frank26080115/Hot-Wand/electrical/hot-wand.sch_preview.pdf

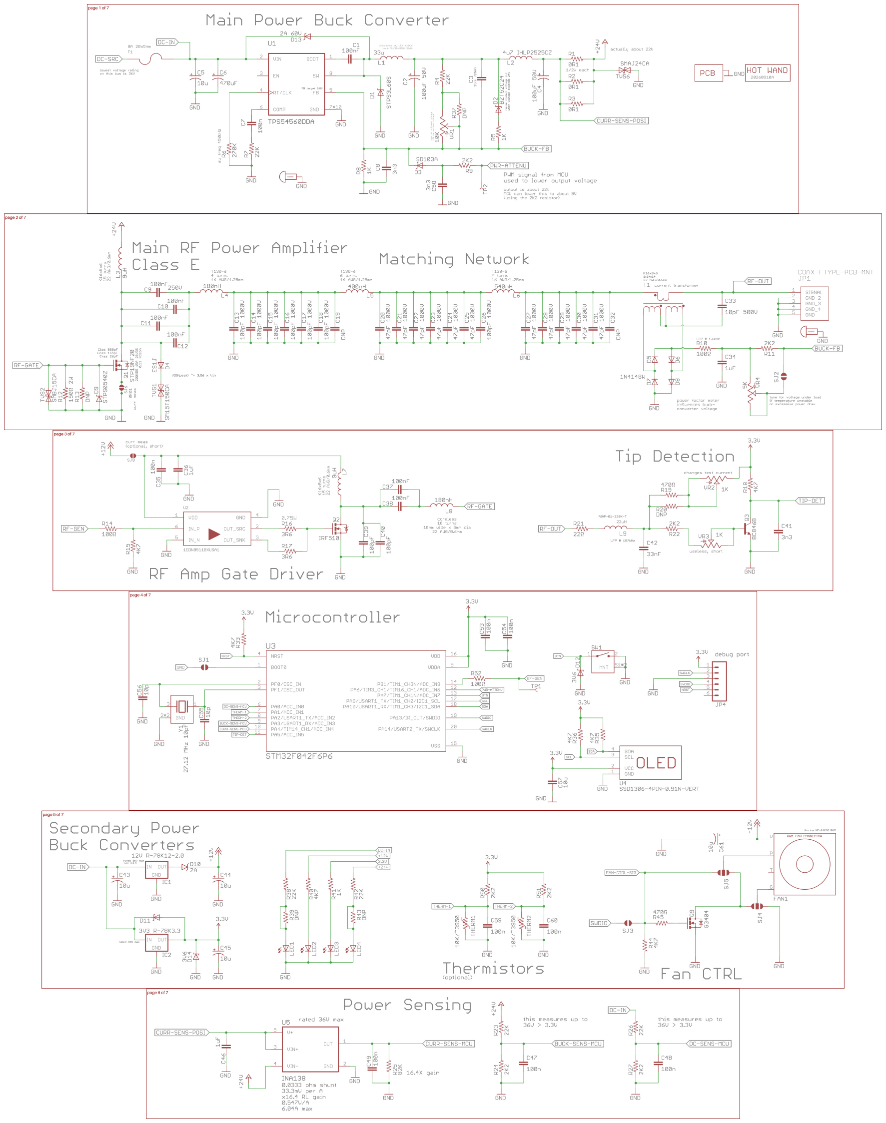
[picture p39: page 1]

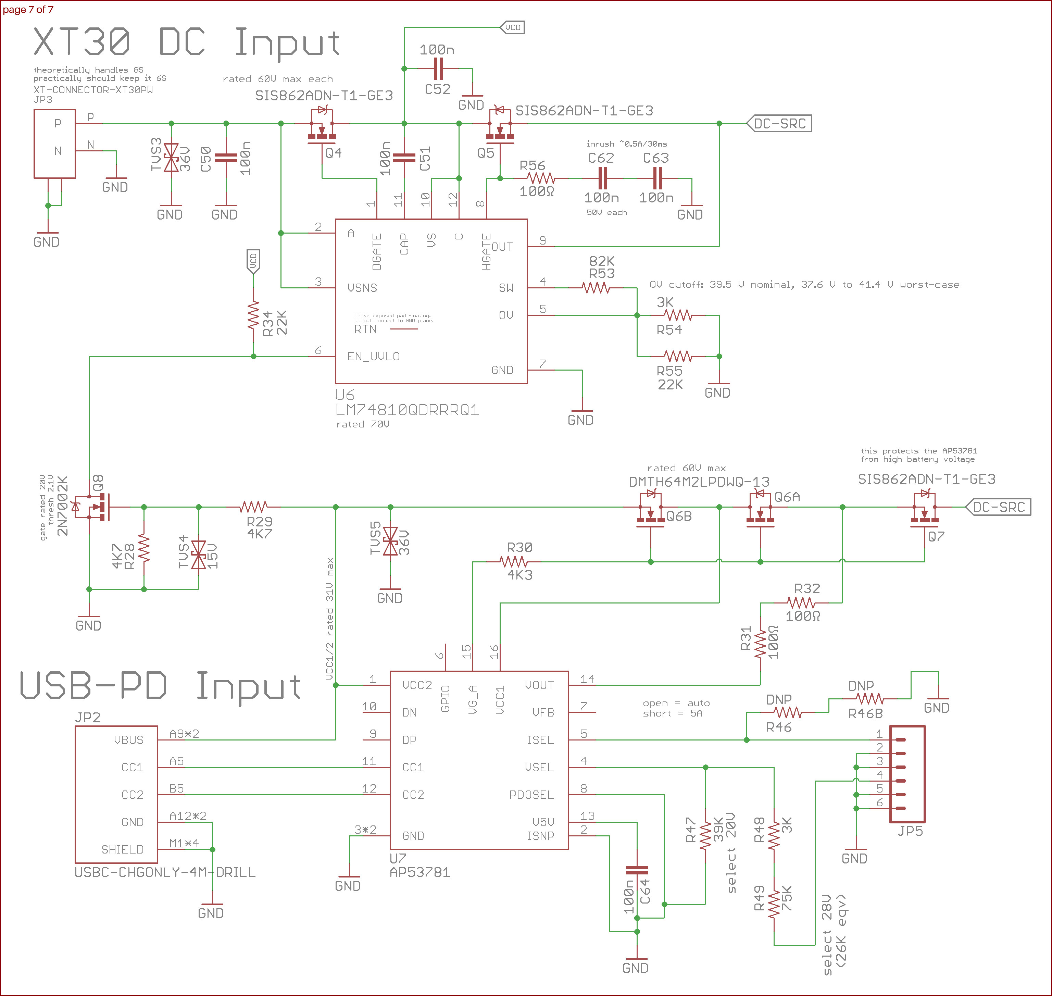
[picture p40: figure]
