frank26080115/Hot-Wand/electrical/hot-wand-lite.sch_preview.pdf

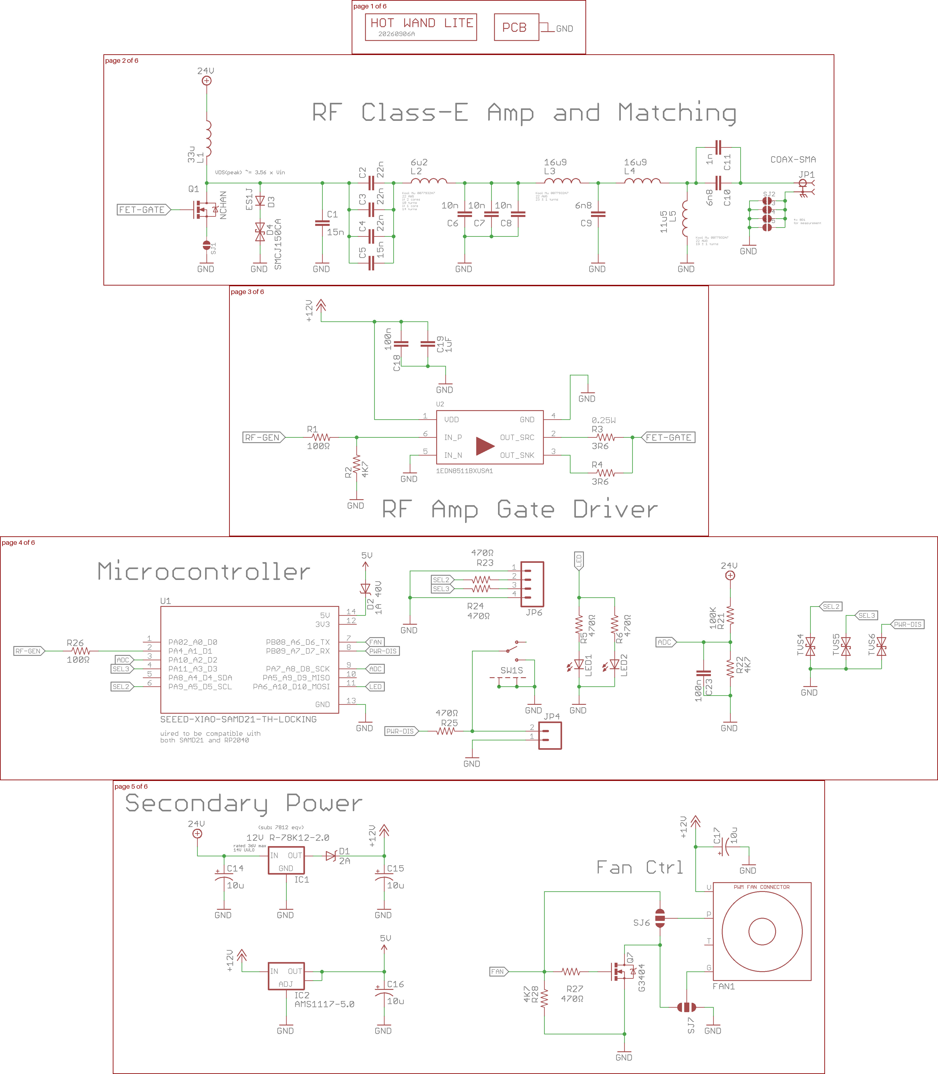
[picture p41: page 1]

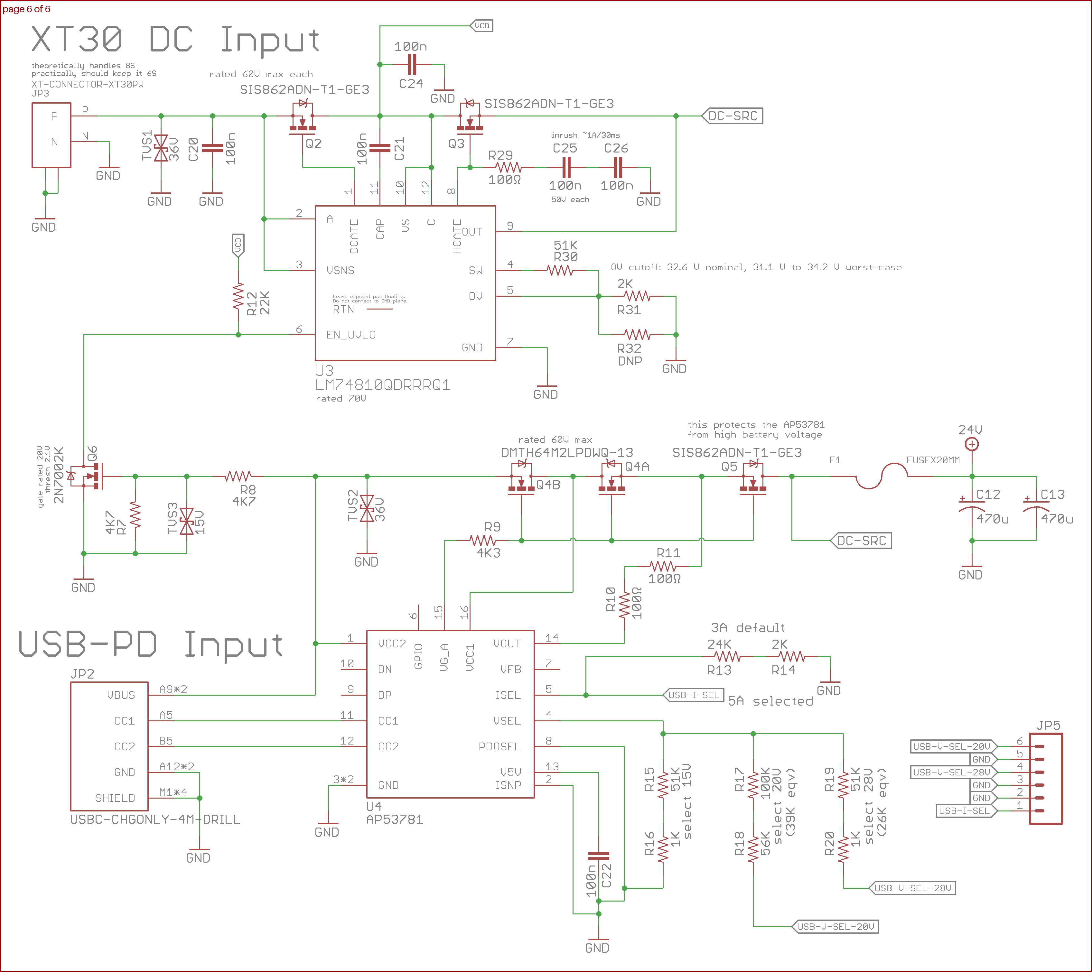
[picture p42: figure]
