frank26080115/Hot-Wand/doc/design-study/sim-470khz/overtemperature/duty.csv

label | tip | frequency_Hz | ptip | pin | pq | vpeak | vturn_3V | vturn_max_3V | iq_peak | cout_rms_A | cout_peak_V | settle_change
D30 | cold | 470000.0 | 15.2460892255 | 31.6820685661 | 13.6332232027 | 66.0378219717 | 58.740601634491824 | 58.790650806476826 | 91.74689067939352 | 1.1465155950586285 | 77.86099760184408 | -0.0002586320019942745
D35 | cold | 470000.0 | 27.8511892675 | 44.5464677931 | 12.4165617244 | 73.4204599296 | 52.99617693522123 | 53.034207180420864 | 84.26761203744175 | 1.5496114778329617 | 103.50217958498992 | 6.62253613330499e-05
D40 | cold | 470000.0 | 43.839329264 | 59.0112184001 | 9.07199362702 | 79.0444573505 | 40.348435256897474 | 40.38910875670194 | 67.48741435793191 | 1.944164979972991 | 125.91700755865497 | 0.00023527174681081675
D45 | cold | 470000.0 | 58.3940621923 | 71.6314488854 | 5.44397941609 | 83.6173232381 | 22.32048153011515 | 22.348759915549376 | 43.61757043852841 | 2.2438069070625146 | 143.65586091826634 | 4.348289923683524e-06
D47.5 | cold | 470000.0 | 63.1862314165 | 75.8699553154 | 4.30991338751 | 85.0733932421 | 12.956661549493777 | 12.975770965911684 | 30.13291947995617 | 2.3340615523982677 | 149.12999289719176 | 3.3242024291002537e-05
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
