frank26080115/Hot-Wand/doc/design-study/sim-470khz/overtemperature/inductors.csv

label | tip | frequency_Hz | ptip | pin | pq | vpeak | vturn_3V | vturn_max_3V | iq_peak | cout_rms_A | cout_peak_V | settle_change
baseline | cold | 470000.0 | 65.7724614815 | 78.2634268863 | 3.78757391316 | 85.8123798694 | 4.903648211298206 | 4.911344844539766 | 30.13291947995617 | 2.381348449450267 | 152.02446680378642 | -1.7534833572918629e-06
L2_-5% | cold | 470000.0 | 74.8583306088 | 91.3728903754 | 6.20488874992 | 82.5457297478 | 18.560682668685228 | 18.59483694554503 | 36.75802010978948 | 2.5405185681576437 | 161.5283471495771 | 0.0001229292416855543
L2_+2% | cold | 470000.0 | 60.7891149073 | 71.9417979183 | 3.22813133709 | 86.2358808974 | 1.4561562750915082 | 1.4658743464604655 | 30.70574819863137 | 2.2893585767824733 | 146.5096551716814 | 2.010327300627779e-06
L2_+5% | cold | 470000.0 | 53.1964953746 | 62.6157434585 | 2.62191636593 | 87.0986545869 | -0.7160607807450767 | -0.7142148700238609 | 30.602989040333167 | 2.1416195234743243 | 138.15701628123037 | 2.0345637539165295e-06
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
