frank26080115/Hot-Wand/doc/design-study/imgs/current_transformer_plots/90.png

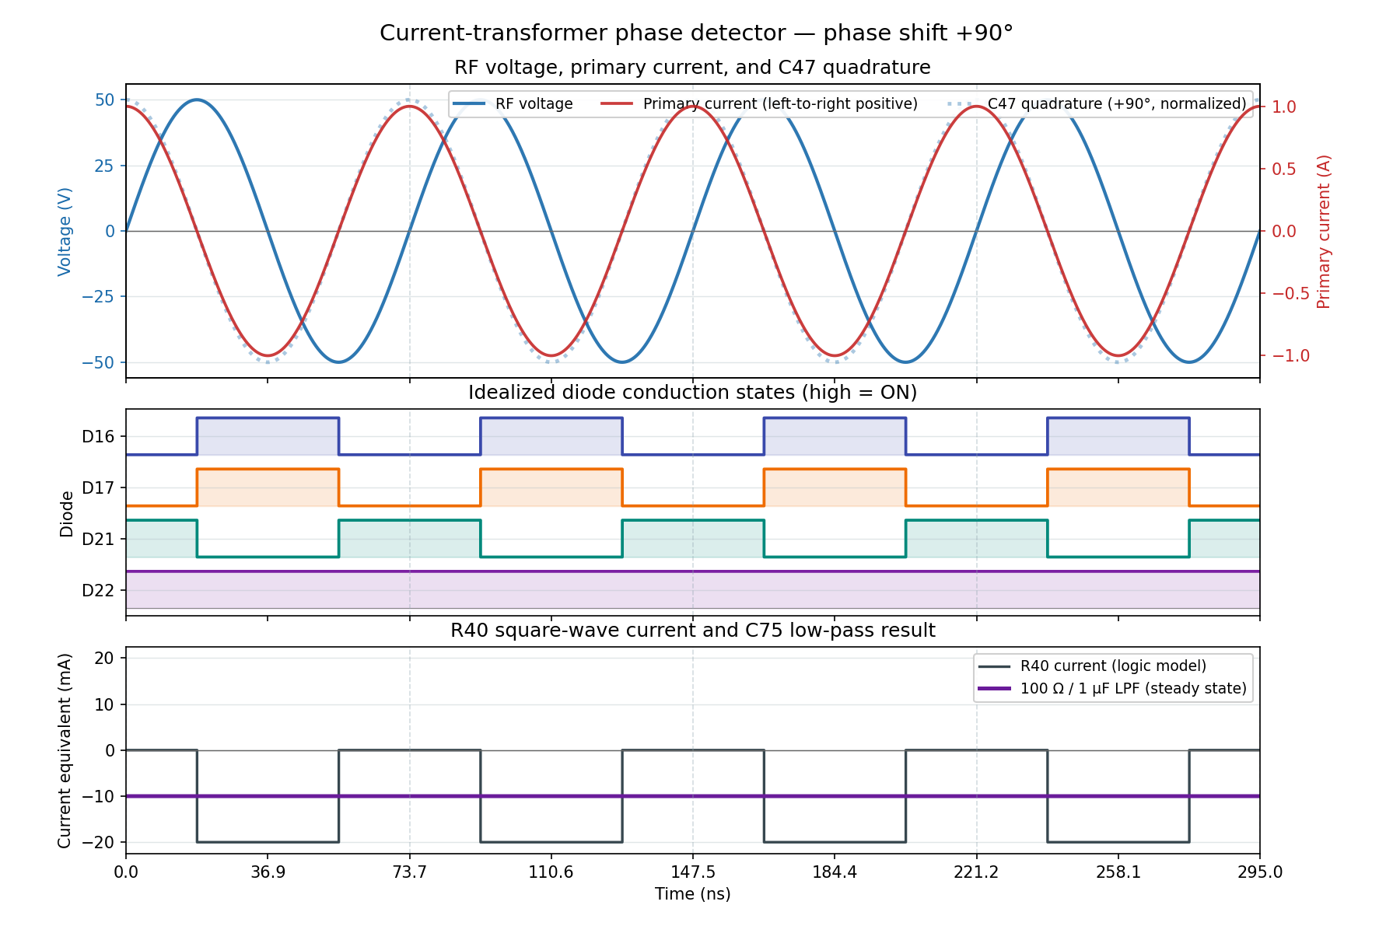
doc/design-study/imgs/current_transformer_plots/90.png
