frank26080115/Hot-Wand/doc/design-study/imgs/current_transformer_plots/225.png

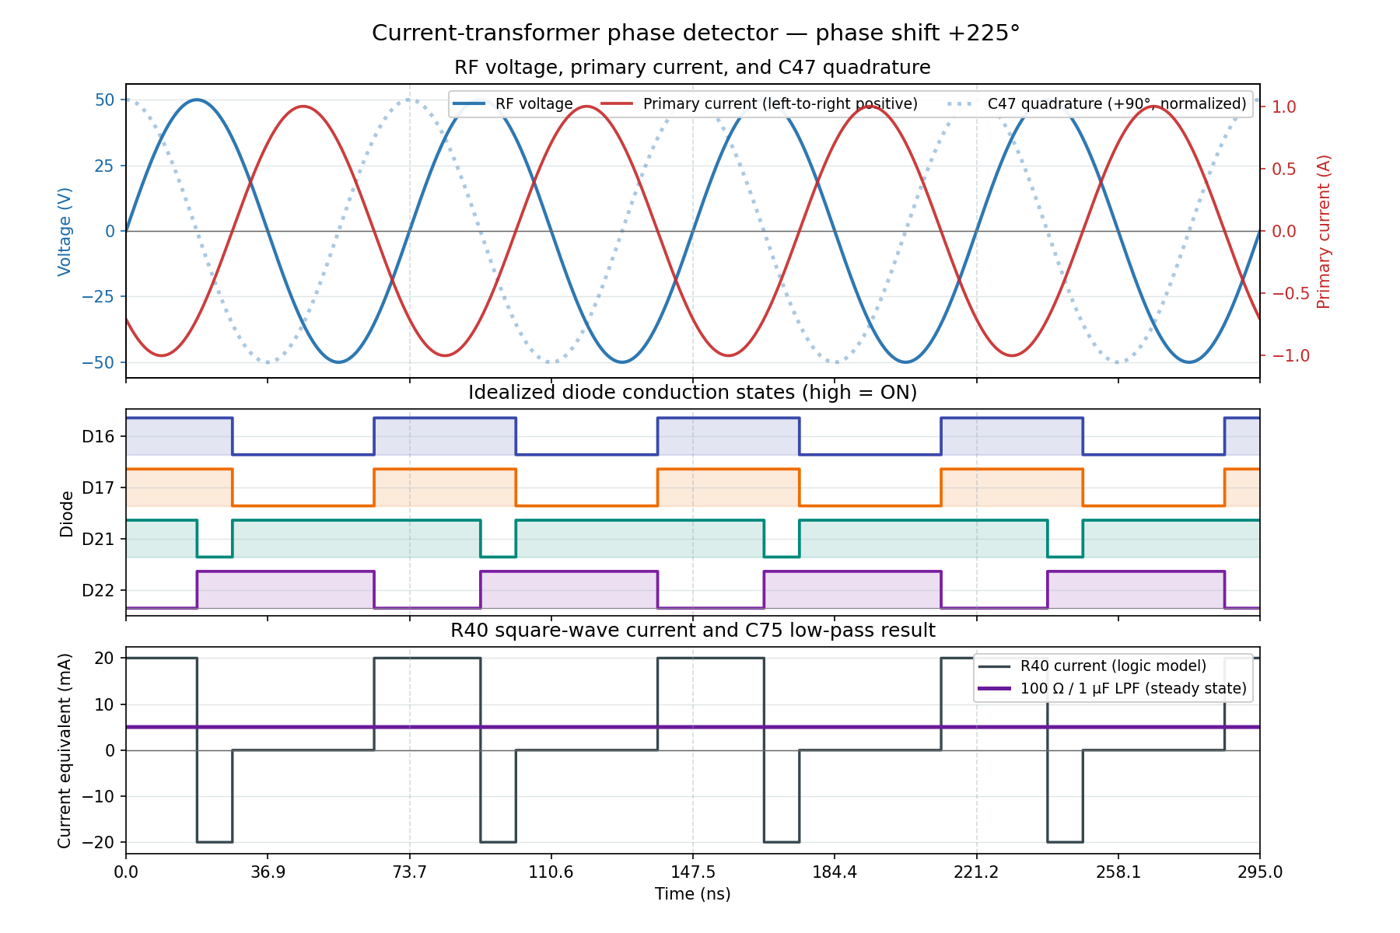
doc/design-study/imgs/current_transformer_plots/225.png
