frank26080115/Hot-Wand/doc/design-study/imgs/current_transformer_plots/345.png

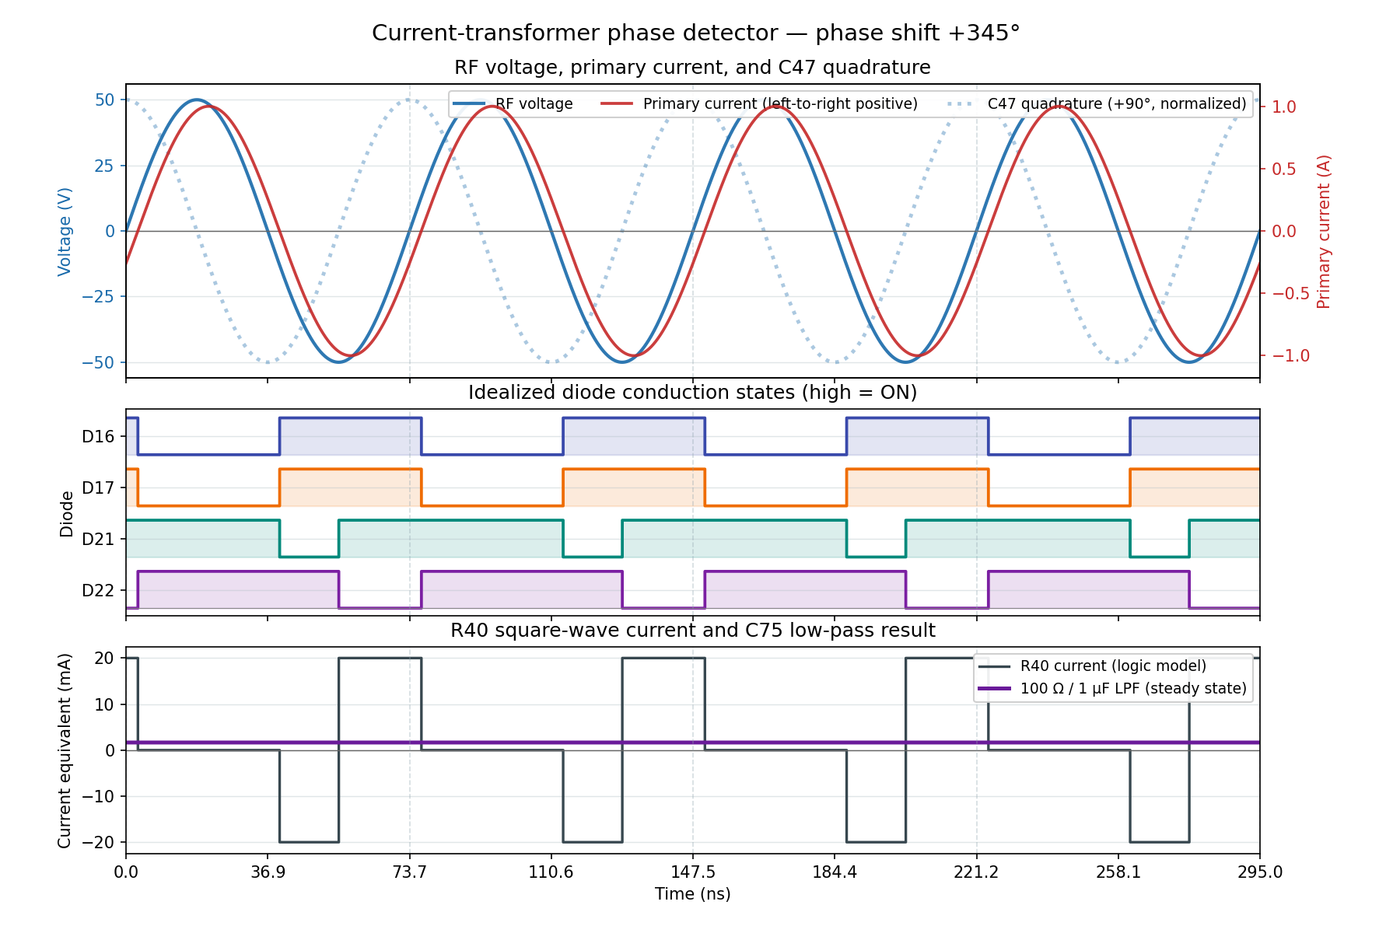
doc/design-study/imgs/current_transformer_plots/345.png
