frank26080115/Hot-Wand/doc/design-study/imgs/tip_det_sim.png

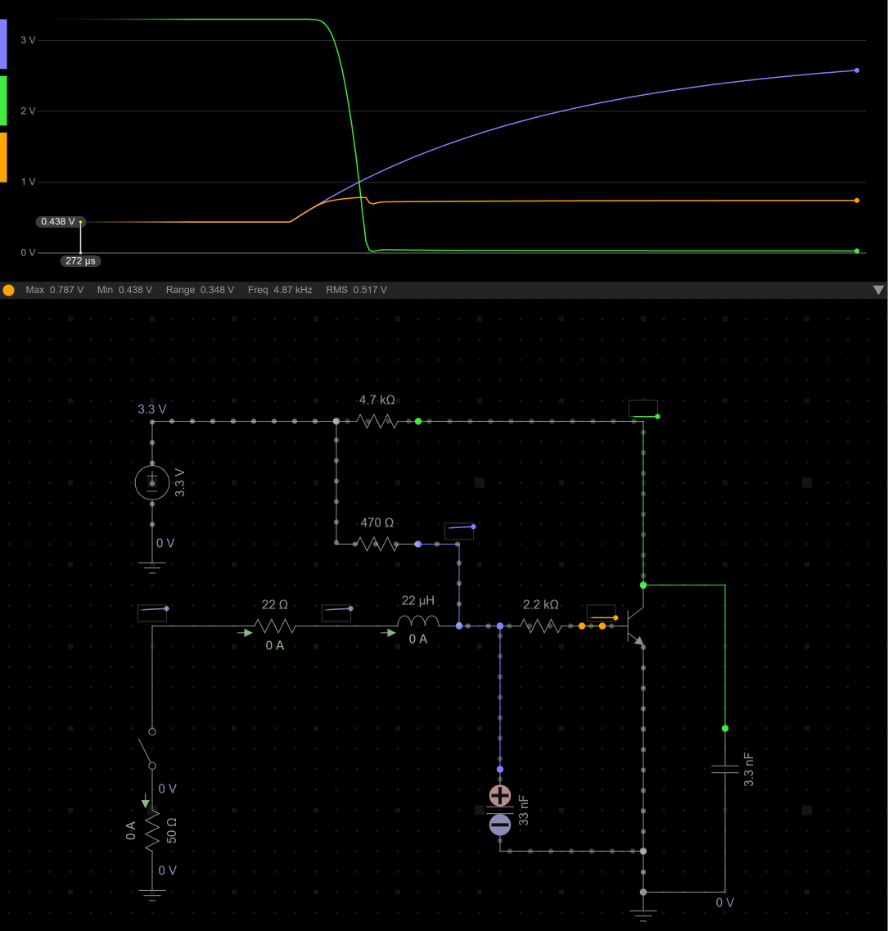
doc/design-study/imgs/tip_det_sim.png
