frank26080115/Hot-Wand/doc/imgs/stand/side_view.png

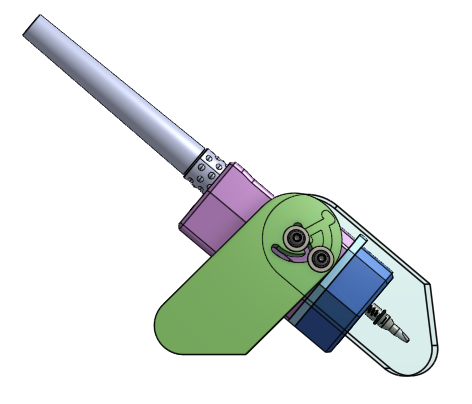
doc/imgs/stand/side_view.png
