frank26080115/Hot-Wand/electrical/mfg-lite/gerbers/illustration-bottom-mirrored.png

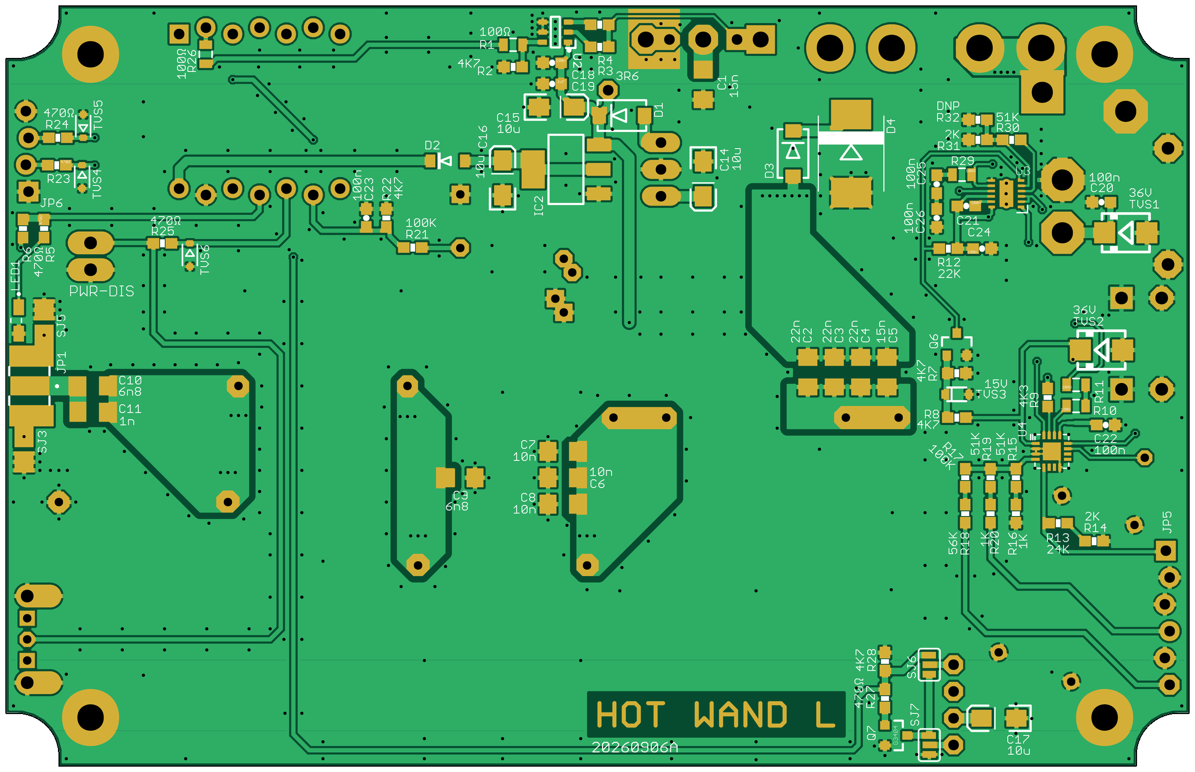
electrical/mfg-lite/gerbers/illustration-bottom-mirrored.png
