frank26080115/Hot-Wand/electrical/mfg-lite/gerbers/illustration-top.png

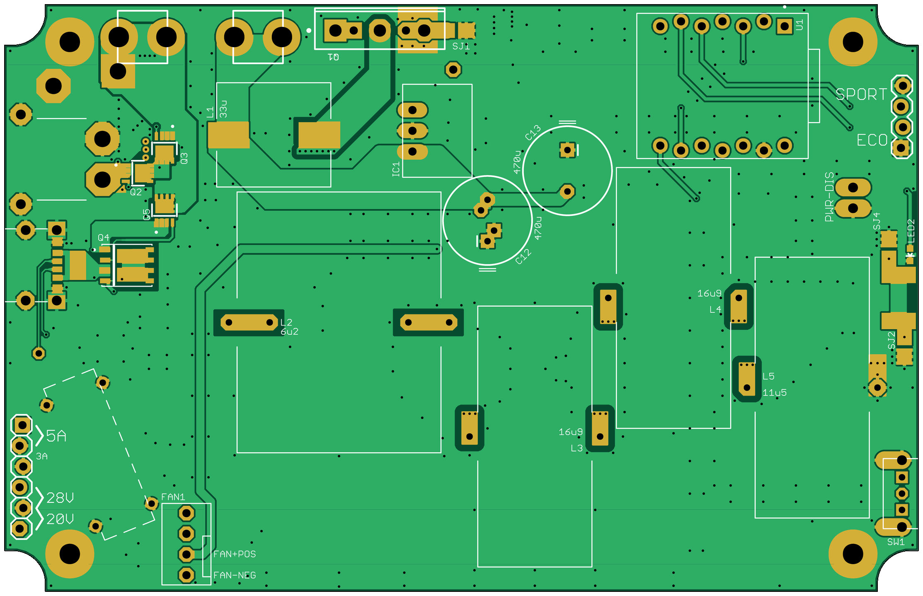
electrical/mfg-lite/gerbers/illustration-top.png
