frank26080115/Hot-Wand/electrical/mfg-lite/gerbers/preview-bottom.png

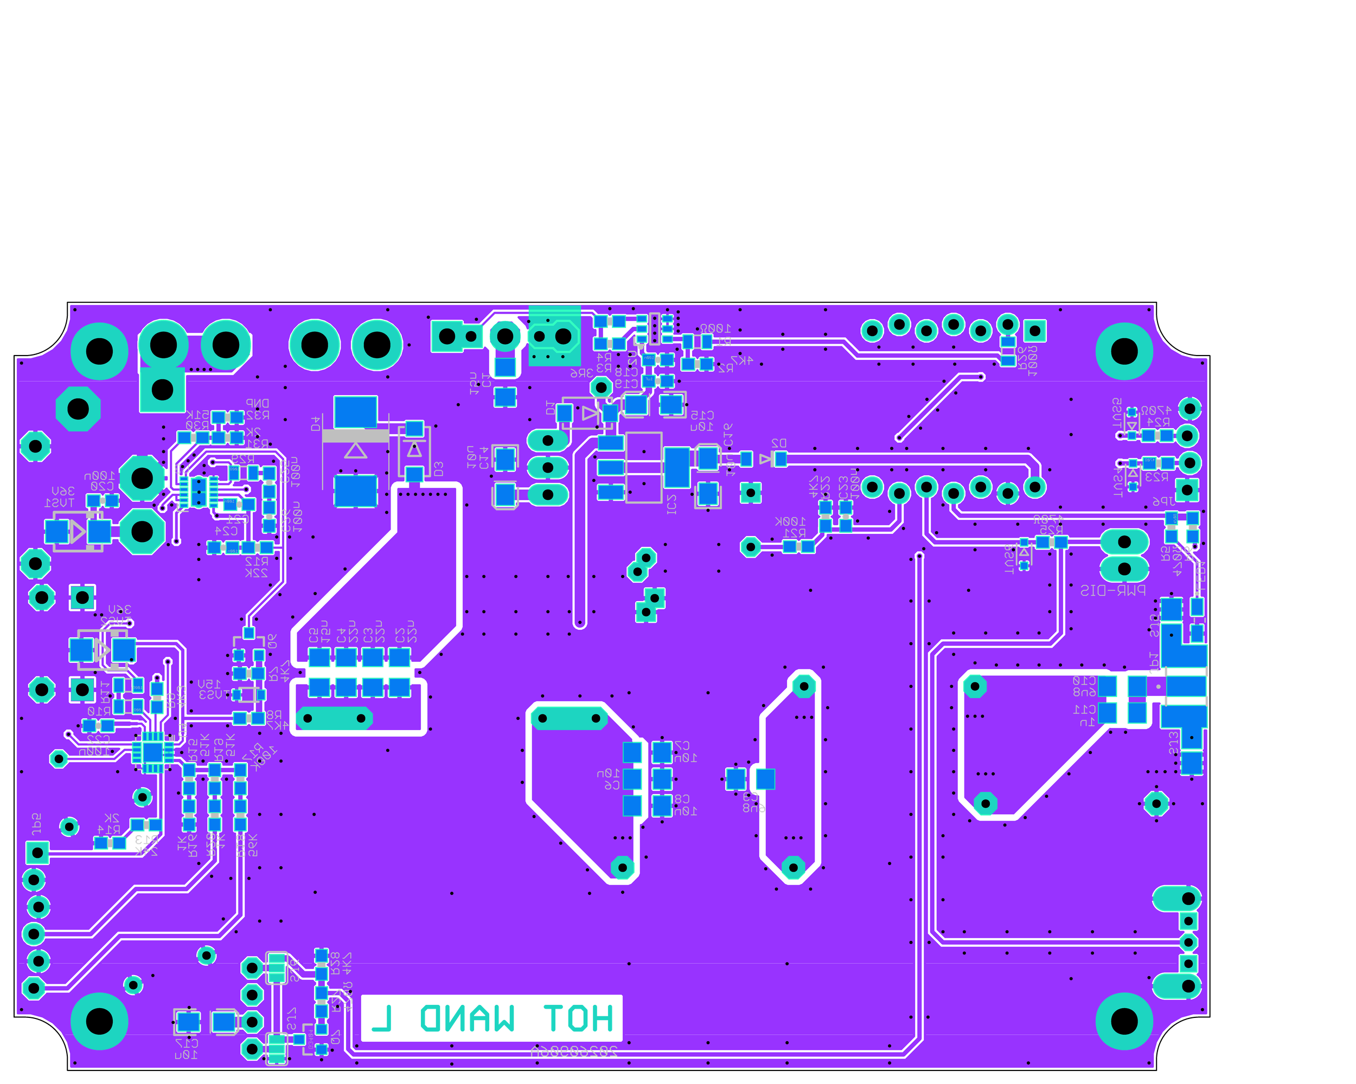
electrical/mfg-lite/gerbers/preview-bottom.png
