frank26080115/Hot-Wand/electrical/mfg-lite/gerbers/preview-top.png

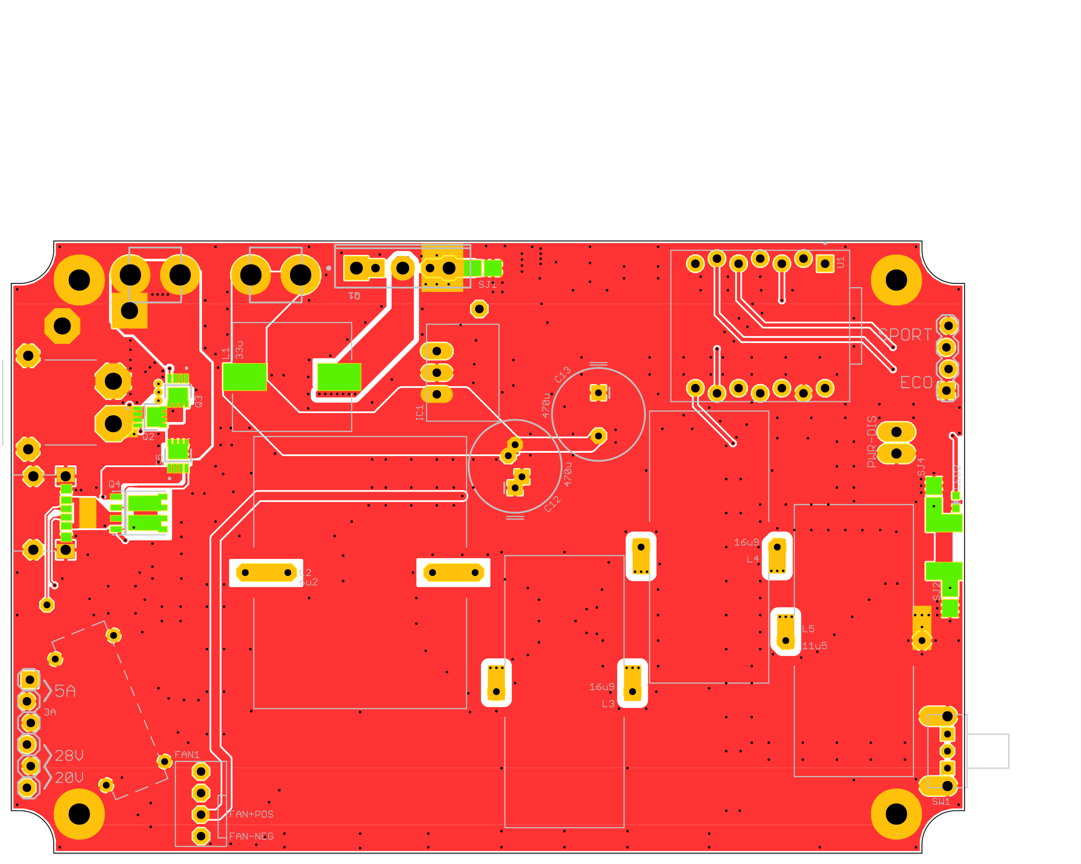
electrical/mfg-lite/gerbers/preview-top.png
