frank26080115/Hot-Wand/electrical/mfg/gerbers/illustration-bottom-mirrored.png

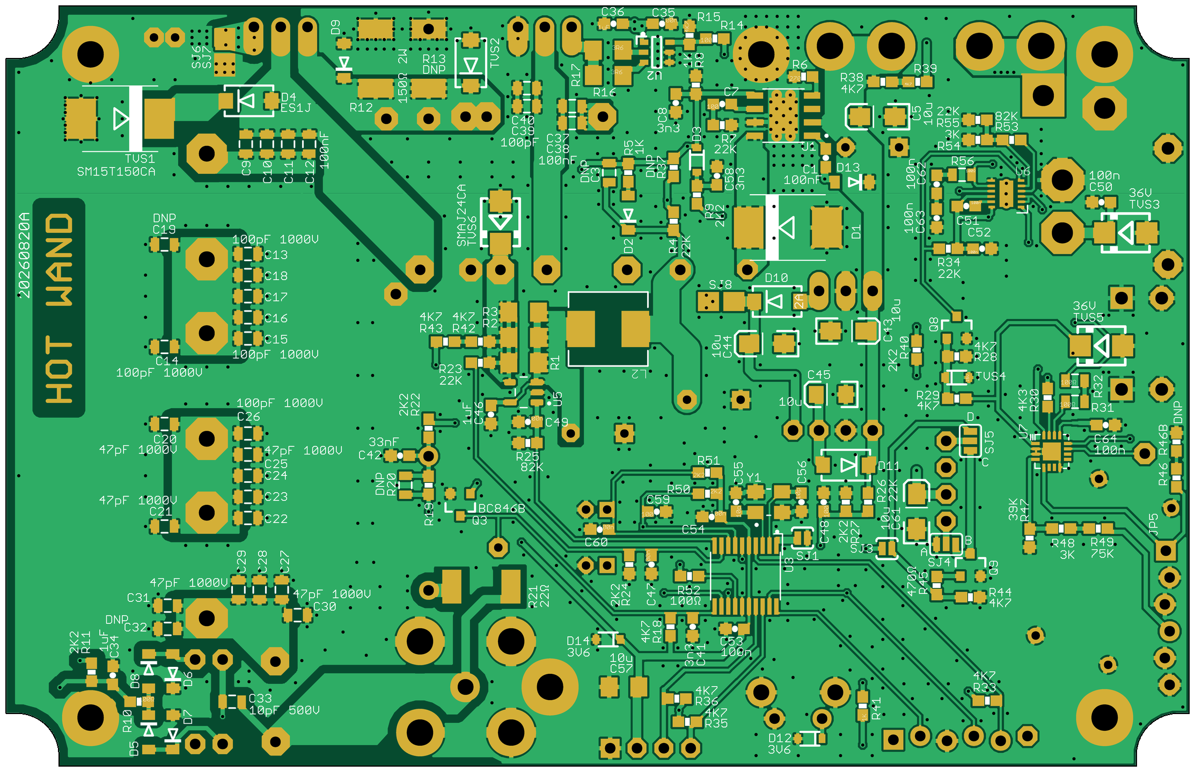
electrical/mfg/gerbers/illustration-bottom-mirrored.png
