frank26080115/Hot-Wand/electrical/mfg/gerbers/illustration-top.png

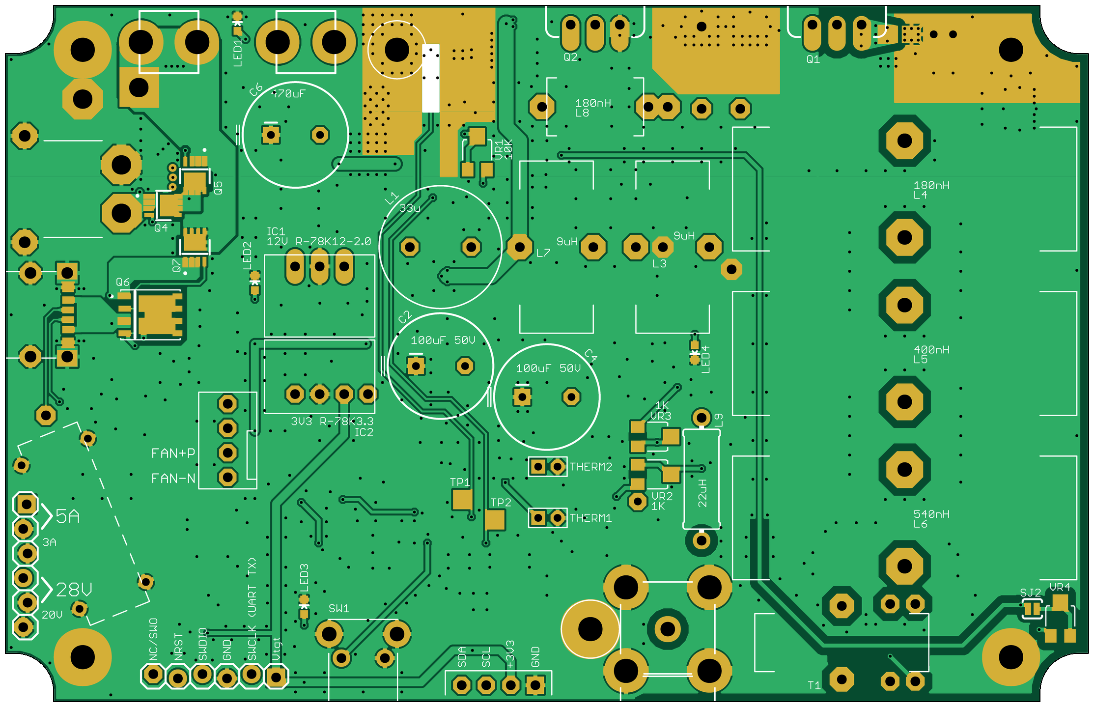
electrical/mfg/gerbers/illustration-top.png
