frank26080115/Hot-Wand/electrical/mfg/gerbers/preview-bottom-mirrored.png

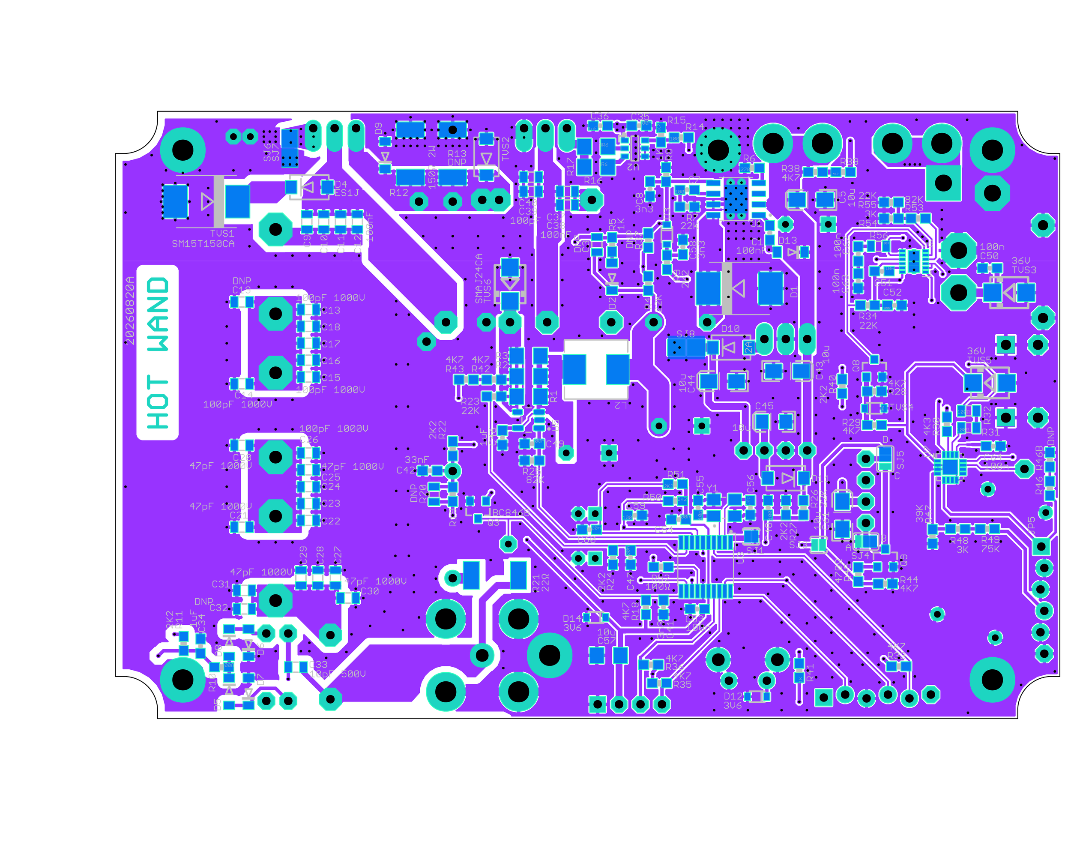
electrical/mfg/gerbers/preview-bottom-mirrored.png
