frank26080115/Hot-Wand/electrical/mfg/gerbers/preview-bottom.png

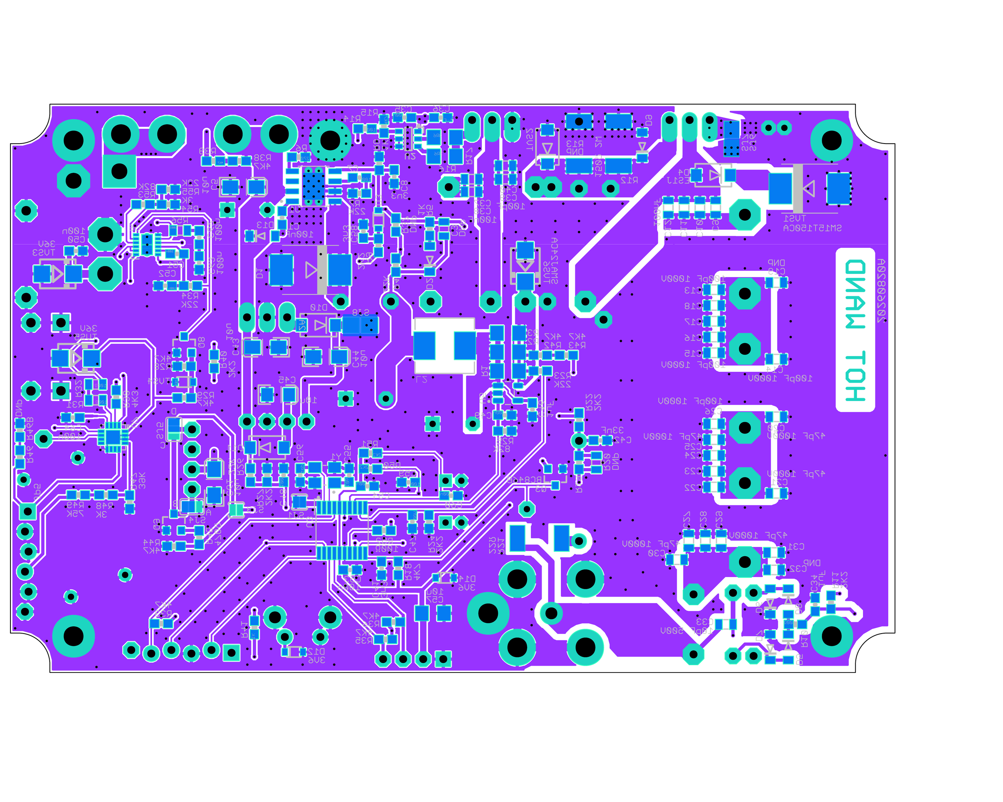
electrical/mfg/gerbers/preview-bottom.png
