frank26080115/Hot-Wand/electrical/mfg/gerbers/preview-top.png

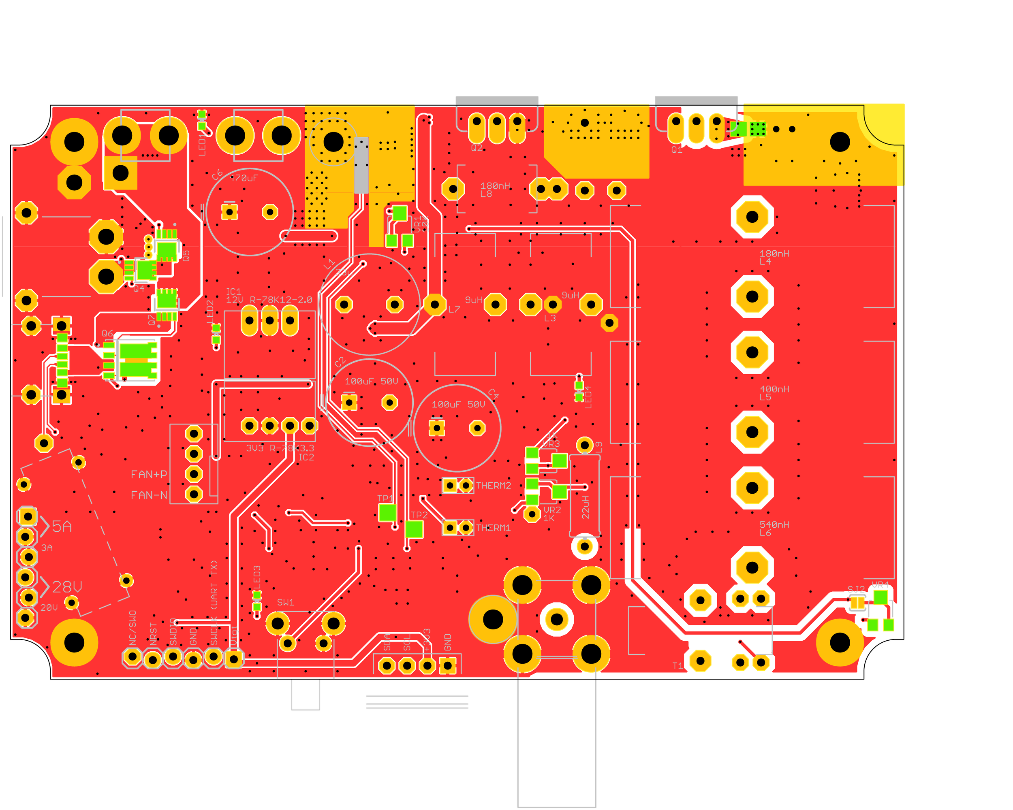
electrical/mfg/gerbers/preview-top.png
