frank26080115/Hot-Wand/firmware/art/fiducial_x8.png

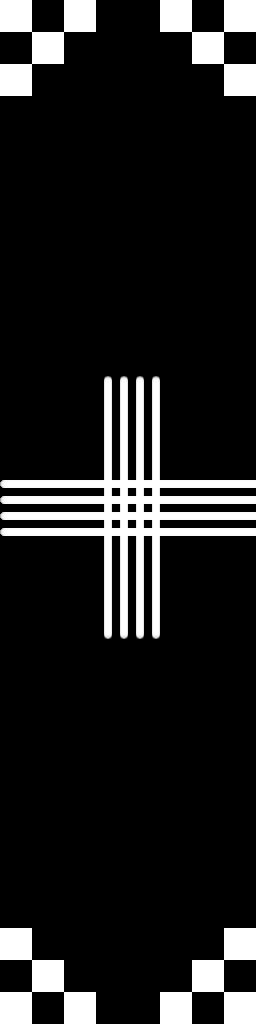
firmware/art/fiducial_x8.png
