frank26080115/Hot-Wand/doc/imgs-shopping/small/zipties.jpg

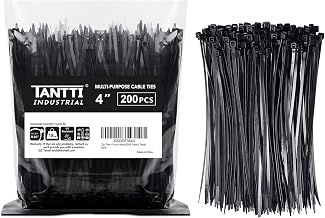
doc/imgs-shopping/small/zipties.jpg
