frank26080115/Hot-Wand/mechanical/main/heatsink-exhaust-duct.step

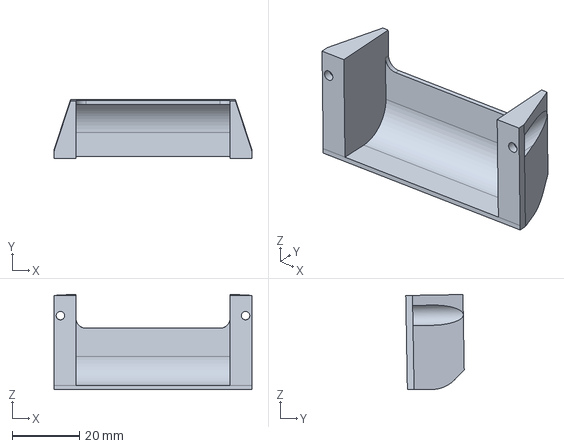
[picture p141: CAD file, 2026-09-05]
mechanical/main/heatsink-exhaust-duct.step
58.8 x 17.4 x 28.2 mm
