frank26080115/Hot-Wand/mechanical/stand/alu-strike-plate.step

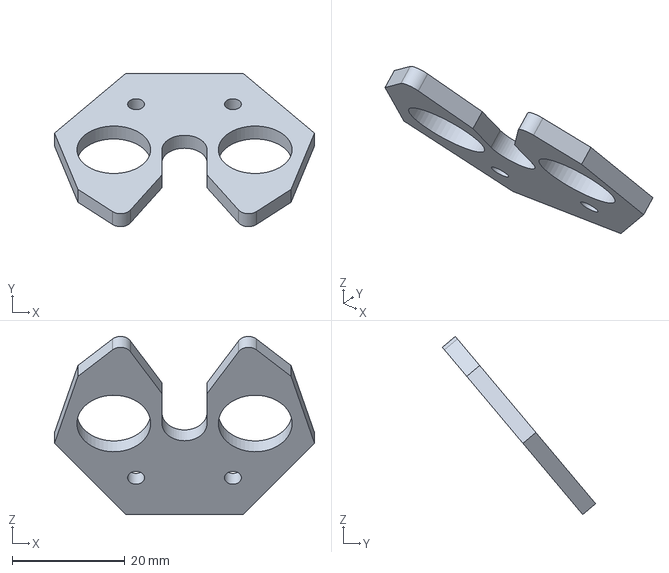
[picture p142: CAD file, 2026-09-03]
mechanical/stand/alu-strike-plate.step
46.1 x 27.2 x 31.6 mm
