frank26080115/Hot-Wand/mechanical/main/air-intake-grille.step

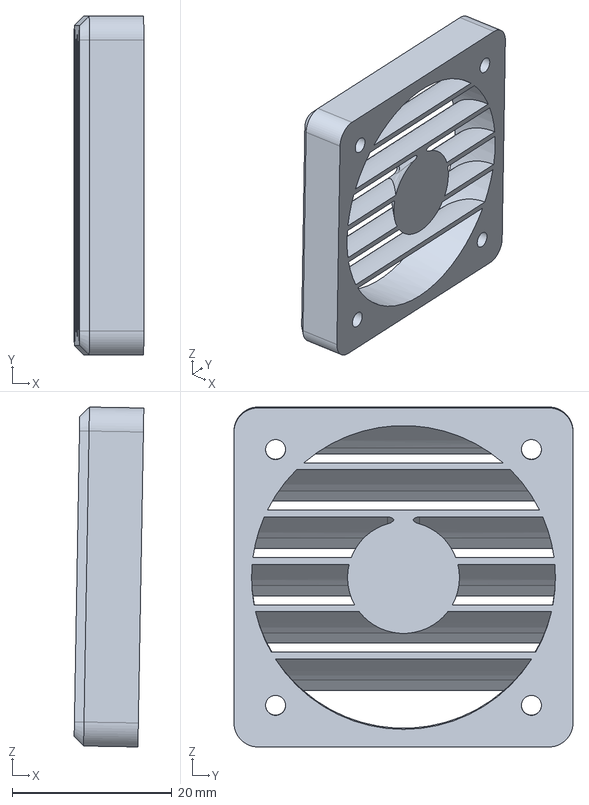
[picture p143: CAD file, 2026-09-05]
mechanical/main/air-intake-grille.step
8.72 x 42.4 x 42.5 mm
