frank26080115/Hot-Wand/mechanical/main/box-template.step

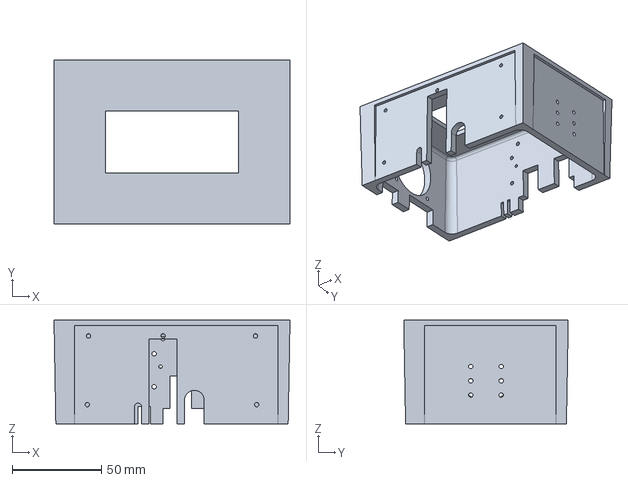
[picture p144: CAD file, 2026-09-05]
mechanical/main/box-template.step
132.0 x 92.0 x 58.0 mm
