frank26080115/Hot-Wand/mechanical/main/face-plate.step

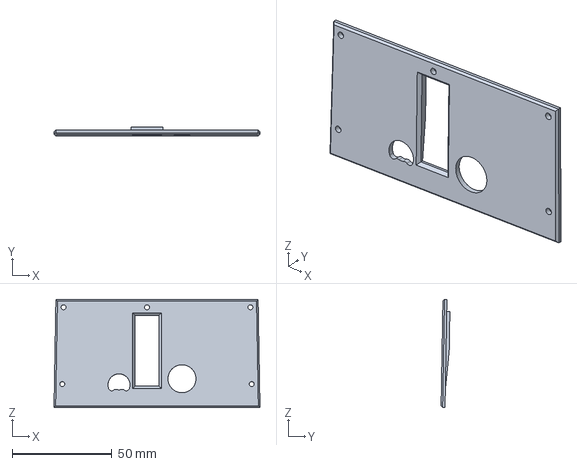
[picture p145: CAD file, 2026-09-05]
mechanical/main/face-plate.step
103.0 x 4.43 x 54.1 mm
