frank26080115/Hot-Wand/mechanical/main/1590t-enclosure-lid.step

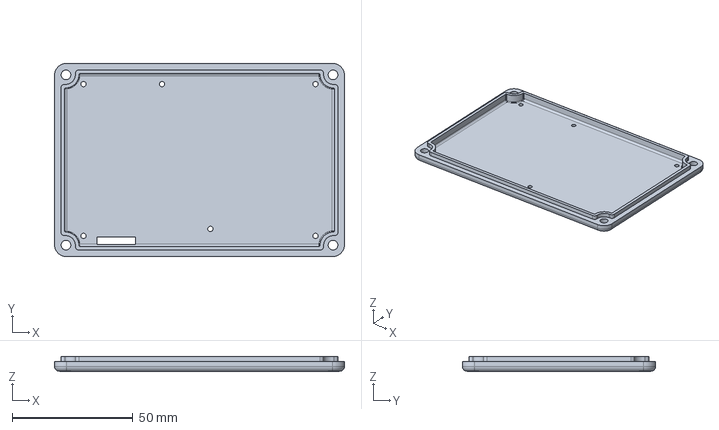
[picture p146: CAD file, 2026-09-05]
mechanical/main/1590t-enclosure-lid.step
120.0 x 80.0 x 6.00 mm
