frank26080115/Hot-Wand/doc/build-guide-13mhz/imgs/mosfets_screws_in_context.png

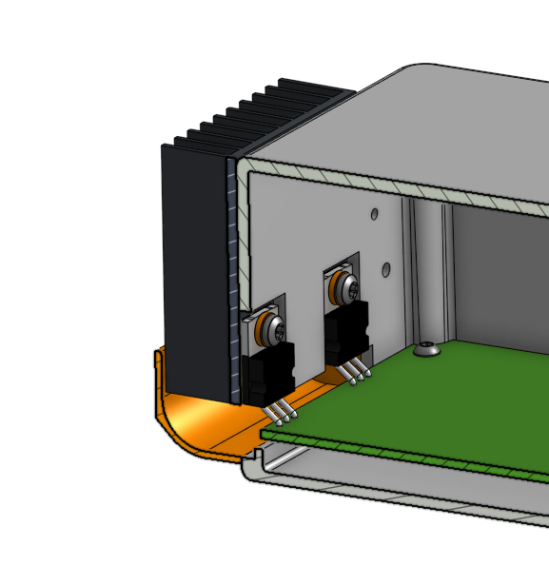
doc/build-guide-13mhz/imgs/mosfets_screws_in_context.png
