frank26080115/Hot-Wand/doc/build-guide-lite-470khz/imgs/airintakegrille_labeled.png

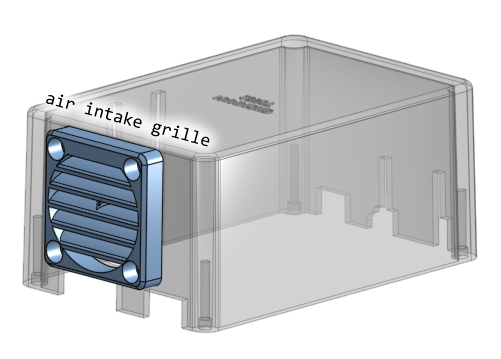
doc/build-guide-lite-470khz/imgs/airintakegrille_labeled.png
