frank26080115/Hot-Wand/doc/build-guide-lite-470khz/imgs/bend_heatsink_fins.png

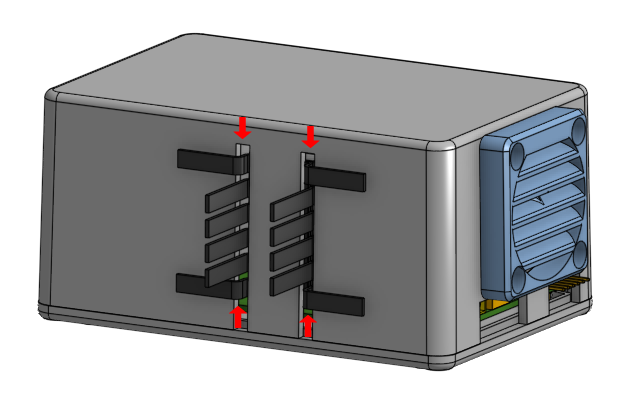
doc/build-guide-lite-470khz/imgs/bend_heatsink_fins.png
