frank26080115/Hot-Wand/doc/build-guide-lite-470khz/imgs/bottom_lid_coax_notch.png

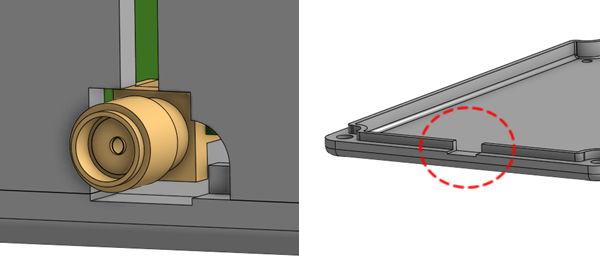
doc/build-guide-lite-470khz/imgs/bottom_lid_coax_notch.png
