frank26080115/Hot-Wand/doc/build-guide-lite-470khz/imgs/cut_template.png

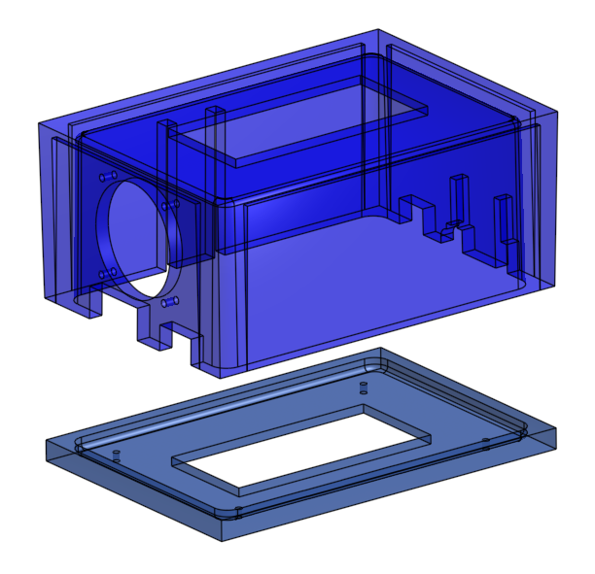
doc/build-guide-lite-470khz/imgs/cut_template.png
