frank26080115/Hot-Wand/doc/build-guide-lite-470khz/imgs/enclosure_opening_labels.png

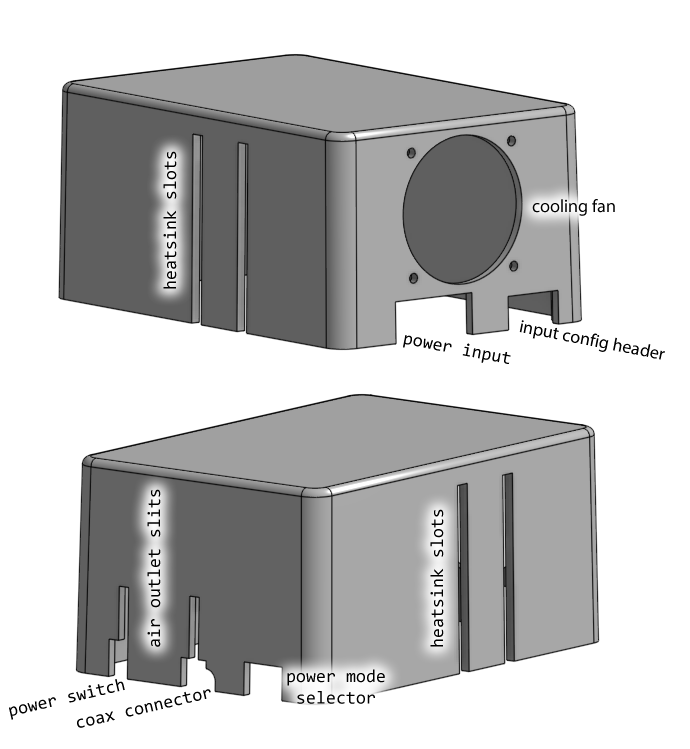
doc/build-guide-lite-470khz/imgs/enclosure_opening_labels.png
