frank26080115/Hot-Wand/doc/build-guide-lite-470khz/imgs/heatsink_sticking_out.png

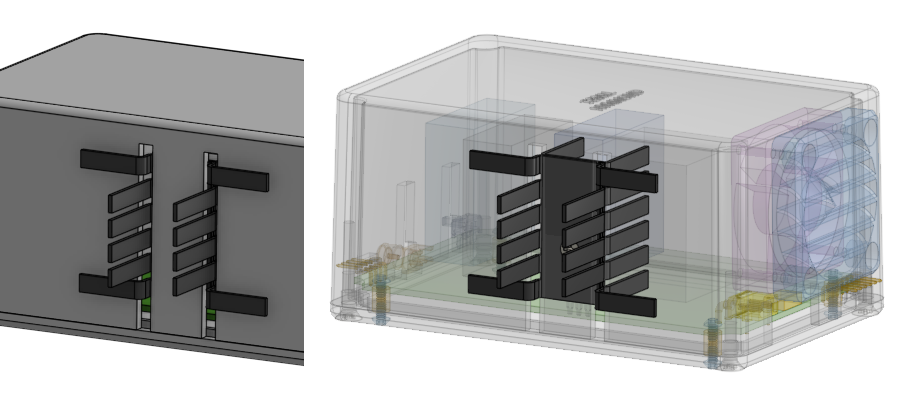
doc/build-guide-lite-470khz/imgs/heatsink_sticking_out.png
