frank26080115/Hot-Wand/doc/build-guide-lite-470khz/imgs/screw_in_lid.png

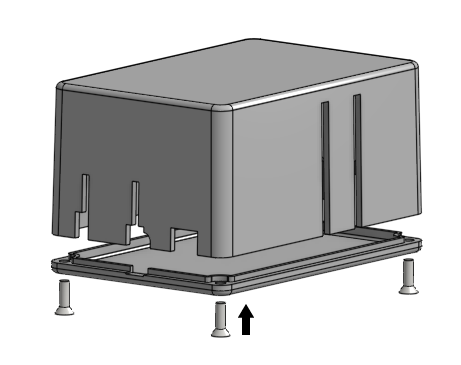
doc/build-guide-lite-470khz/imgs/screw_in_lid.png
