frank26080115/Hot-Wand/doc/build-guide-lite-470khz/imgs/standoffs_3d.png

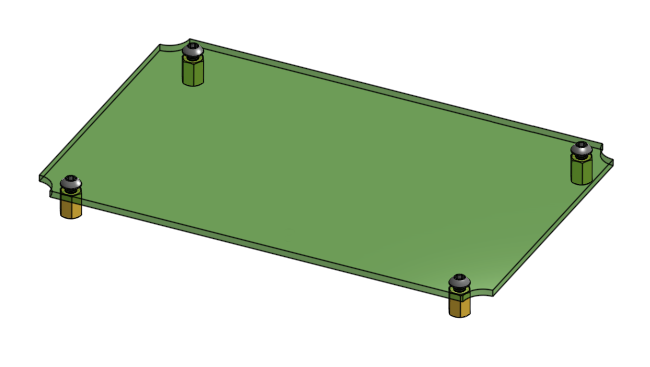
doc/build-guide-lite-470khz/imgs/standoffs_3d.png
