frank26080115/Hot-Wand/doc/design-study/sim-470khz/overtemperature/duty_verify.csv

label | tip | frequency_Hz | ptip | pin | pq | vpeak | vturn_3V | vturn_max_3V | iq_peak | cout_rms_A | cout_peak_V | settle_change
D10 | cold | 470000.0 | 1.02616176361 | 7.09332360097 | 5.56444951707 | 42.7522142597 | 40.41561128628378 | 40.415611286554245 | 62.45704079762196 | 0.29743110486960256 | 19.420209796154715 | -2.0405414235757924e-05
D15 | cold | 470000.0 | 1.84912271091 | 9.8271539371 | 7.21089590293 | 49.5783152028 | 45.804233203197846 | 45.82872722425273 | 70.5944279052049 | 0.39926520490652 | 26.285502930731298 | 5.573209831721826e-05
D20 | cold | 470000.0 | 3.65251913777 | 14.4902280082 | 9.69341063917 | 58.2367676011 | 52.327120506367976 | 52.32714108481091 | 80.06398556750406 | 0.5611447650541777 | 37.48644146843888 | 3.5121441444019297e-07
D25 | cold | 470000.0 | 7.51634361989 | 21.871964639 | 12.5363280771 | 65.0831804076 | 58.27588865600345 | 58.28182411037042 | 89.20658874458124 | 0.8049741657788082 | 54.478589315291934 | 4.691037518433916e-06
D40 | cold | 470000.0 | 43.7881054841 | 58.9787618981 | 9.0615828276 | 79.0333266677 | 40.35123349634367 | 40.35836946489837 | 68.2905736331988 | 1.9429284981488195 | 125.88910498819465 | -3.052191714147945e-06
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
