frank26080115/Hot-Wand/doc/design-study/sim-13mhz/rf_amp_with_tvs_clamp.asc

C9_12: cap; 400n; Rser={Rcap}
C13_18: cap; 600p; Rser={Rcap}
C20_26: cap; 382p; Rser={Rcap}
C27_31: cap; 235p; Rser={Rcap}
C_TVS: cap; {Ctvs}
Ctip: cap; {C_tip}; Rser=0 Rpar={if(TipState==2,1e12,1u)}
D4: diode; ES1J_EST
DTVS1: TVSdiode; SM15T150CA_EST
L3: ind; 9u; Rser={Rchoke} Rpar=1G
L4: ind; 180n; Rser={Rcoil} Rpar=1G
L5: ind; 400n; Rser={Rcoil} Rpar=1G
L6: ind; 540n; Rser={Rcoil} Rpar=1G
Ltip: ind; {L_tip}; Rser=1u
M1: nmos; STP19NF20_EST
Rtip: res; {R_tip}
Vcc: voltage; {VCC}
Vdrive: voltage; PULSE(0 {Vgate} 0 {Tedge} {Tedge} {Duty/Freq-Tedge} {1/Freq})
Named nets: Vds, Clamp, 0, Vdc, Vgs, ACcoupled, Filter1, Filter2, RFout, Rtip
VDS clamp from electrical/hot-wand.sch
ES1J anode at Vds; cathode at Clamp
SM15T150CA between Clamp and ground
C_TVS represents TVS capacitance.
Hot-Wand 13.56 MHz final RF stage - ES1J / SM15T150CA VDS clamp
Circuit: electrical/hot-wand.sch. Buck = ideal DC Vcc; Q1 = M1; driver stage and current transformer omitted.
C9-C12 = 4 x 100n; C13-C18 = 6 x 100p
C20-C26 = 6 x 47p + 100p; C27-C31 = 5 x 47p
C19 and C32 are DNP. D4/TVS1 clamp branch included.
STTC-147 at 13.56 MHz (current-transformer.md)
TipState 1: Cold = 42.3 + j13 ohm
TipState 2: Warm = 55 - j16 ohm
TipState 3: Hot = 12 + j24 ohm
TipState 4: Open = 1e12 ohm
L/C calculated from reactance at Freq.
.param Freq=13.56Meg Vgate=12 Duty=0.5 Tedge=2n
.param Rchoke=0.1 Rcoil=0.03 Rcap=0.01
.param R_tip=table(TipState,1,42.3,2,55,3,12,4,1e12)
.param L_tip=table(TipState,1,13/(2*pi*Freq),2,1p,3,24/(2*pi*Freq),4,1p)
.param C_tip=if(TipState==2,1/(2*pi*Freq*16),1p)
.step param VCC list 15 20 25 30
.step param TipState list 1 2 3 4
.param Tstop=1m Tsettle=980u Tmax=200p
.tran 0 {Tstop} 0 {Tmax} startup
.options plotwinsize=0 numdgt=7 reltol=1e-4
.temp 25
.meas TRAN V_DS MAX V(Vds)
.meas TRAN V_DS_LAST MAX V(Vds) FROM {Tsettle} TO {Tstop}
.meas TRAN V_DS_PREV MAX V(Vds) FROM {Tsettle-20u} TO {Tsettle}
.save V(Vds) V(Vgs) V(Clamp) I(D4) I(DTVS1)
V_DS = maximum over the full run, including the 20 us LTspice startup ramp.
V_DS_LAST / V_DS_PREV compare the final two 20 us windows.
No tip is open at the PCB output; no cable transmission line is modeled.
Unused Ctip is bypassed by 1u ohm; warm Ctip leakage is 1e12 ohm.
Ltip=1pH bypasses unused L; its series loss is 1u ohm.
Rchoke/Rcoil/Rcap are assumed losses, not measured RF values.
STP19NF20_EST is a datasheet-based approximation, NOT an ST vendor model.
Nominal targets: Vth=3V; Ron~0.11 ohm at Vgs=10V; Ciss~800p, Coss~165p, Crss~26p at Vds=25V.
Rg=2 ohm, Kp=7 and body-diode parameters are estimates. No avalanche or self-heating model.
Gate is ideal 0-12V with 2ns edges and 50% duty; the real resonant gate waveform is not reproduced.
.model STP19NF20_EST VDMOS(Vto=3 Kp=7 Rd=85m Rs=5m Rg=2 Rb=0.1 Cgs=774p Cgdmin=10p Cgdmax=550p A=0.43 Cjo=789p Vj=0.8 M=0.5 Is=10p N=1.3 Tt=65n)
Same MOSFET/gate/network assumptions as rf_amp.asc. Only the drain clamp is added.
Diodes are datasheet-based approximations, not vendor SPICE models; fixed at 25C, no self-heating or failure.
The TVS knee uses the upper 25C breakdown value, not a typical 150V device.
.param VbrTVS=158 Rtvs=6.81 Ctvs=200p TtES=15n
.model ES1J_EST D(Is=1n N=2 Rs=0.235 Cjo=42.4p Vj=0.7 M=0.4 Tt={TtES} Bv=600 Ibv=5u)
.model SM15T150CA_EST D(Ron={Rtvs} Rrev={Rtvs} Roff=1G Vfwd={VbrTVS} Vrev={VbrTVS} Epsilon=0.01 Revepsilon=0.01)
TVS upper-voltage 10/1000us fit: V ~= 158 + 6.81*I, about 207V at 7.2A.
200pF TVS capacitance is an assumed lumped value; leakage is approximated by 1G ohm.
ES1J fit: Vf~1.3V at 1A, Cj~20pF at 4V. Tt=15ns is an estimate, not its quoted 35ns trr.
Microsecond surge data and estimated diode models are not a validated 13.56MHz clamp model.
.meas TRAN I_TVS_PK MAX I(DTVS1)
.meas TRAN P_TVS AVG (V(Clamp)*I(DTVS1)) FROM {Tsettle} TO {Tstop}
.meas TRAN E_TVS INTEG (V(Clamp)*I(DTVS1))
.meas TRAN P_ES1J AVG (V(Vds,Clamp)*I(D4)) FROM {Tsettle} TO {Tstop}
.meas TRAN I_ES1J_PK MAX I(D4)
.meas TRAN P_TVS_PREV AVG (V(Clamp)*I(DTVS1)) FROM {Tsettle-20u} TO {Tsettle}
P_TVS uses TVS conduction current only.
C_TVS reactive current is excluded from TVS heat.
ES1J terminal power is averaged over final RF cycles.
E_TVS covers the whole 1ms run.
