frank26080115/Hot-Wand/firmware/inc/conf.h

#pragma once

/* Project-wide settings are ordered from frequently tuned behavior to implementation details. */
/* Each validation block stays immediately after the settings it protects. */

// -----------------------------------------------------------------------------
// User Interaction and Setup
// -----------------------------------------------------------------------------

#define SHOW_SPLASH    // the 5 splash screens use about 3 kb of memory
#define SHOW_SPLASH_MS 2000

#if defined(SHOW_SPLASH) && (SHOW_SPLASH_MS == 0)
#error "SHOW_SPLASH_MS must be nonzero when splash screens are enabled"
#endif

#ifndef BTN_LONG_PRESS_MS
#define BTN_LONG_PRESS_MS 1000
#endif

#ifndef BTN_CONSECUTIVE_PRESS_TIMEOUT_MS
#define BTN_CONSECUTIVE_PRESS_TIMEOUT_MS 5000
#endif

#if BTN_CONSECUTIVE_PRESS_TIMEOUT_MS == 0
#error "BTN_CONSECUTIVE_PRESS_TIMEOUT_MS must be nonzero"
#endif

#ifndef SETUP_MENU_TIMEOUT_MS
#define SETUP_MENU_TIMEOUT_MS (5 * 60 * 1000)
#endif

#define SETUP_HOLD_DURATION_MS 3000

#if SETUP_HOLD_DURATION_MS == 0
#error "SETUP_HOLD_DURATION_MS must be nonzero"
#endif

// -----------------------------------------------------------------------------
// Power and Thermal Limits
// -----------------------------------------------------------------------------

#define ADC_REFERENCE_MV      3300UL
#define ADC_FULL_SCALE        1023UL
#define VOLTAGE_DIVIDER_SCALE 11UL
#define ADC_VOLTAGE_TO_COUNTS(millivolts)                                                                              \
    (((millivolts) * ADC_FULL_SCALE + (ADC_REFERENCE_MV * VOLTAGE_DIVIDER_SCALE) - 1UL) /                              \
     (ADC_REFERENCE_MV * VOLTAGE_DIVIDER_SCALE))

#ifndef ADC_VREFINT_SAMPLE_INTERVAL_ROUNDS
#define ADC_VREFINT_SAMPLE_INTERVAL_ROUNDS 1024UL
#endif

#if ADC_VREFINT_SAMPLE_INTERVAL_ROUNDS == 0
#error "ADC_VREFINT_SAMPLE_INTERVAL_ROUNDS must be nonzero"
#endif

#define TEMPERATURE_HOT_WARNING_THRESH_C 80
#define TEMPERATURE_SHUTDOWN_THRESH_C    110
#define TEMPERATURE_SHUTDOWN_TIME_MS     1000
#define TEMPERATURE_HYSTERYSIS_C         5

/* Model parameters, not measured thermal properties: drain 60 W plus stored
 * energy / 20 s. From empty, 80 W reaches warning in about 20.4 s and 100 W
 * in about 7.7 s; 60 W runs indefinitely. At sustained 100 W, energy tends
 * toward 800 J, equivalent to 200 C on the virtual scale. */
#define LEAKY_BUCKET_LEAK_MW             60000UL
#define LEAKY_BUCKET_WARNING_ENERGY_UJ   256000000UL
#define LEAKY_BUCKET_COOLING_TIME_MS      20000UL
#define LEAKY_BUCKET_EMPTY_TEMPERATURE_C 25U

/* 111 C allows the existing >110 C shutdown check to fire. Set this to 81 C
 * to limit the bucket to recoverable derating instead. */
#ifndef LEAKY_BUCKET_MAX_TEMPERATURE_C
#define LEAKY_BUCKET_MAX_TEMPERATURE_C 111U
#endif

#if (LEAKY_BUCKET_MAX_TEMPERATURE_C < TEMPERATURE_HOT_WARNING_THRESH_C + 1U) ||                        \
    (LEAKY_BUCKET_MAX_TEMPERATURE_C > 65535U)
#error "LEAKY_BUCKET_MAX_TEMPERATURE_C must reach the warning and fit in uint16_t"
#endif

#if (LEAKY_BUCKET_LEAK_MW == 0) || (LEAKY_BUCKET_WARNING_ENERGY_UJ == 0) ||                              \
    (LEAKY_BUCKET_COOLING_TIME_MS == 0) ||                                                                \
    (LEAKY_BUCKET_EMPTY_TEMPERATURE_C >= TEMPERATURE_HOT_WARNING_THRESH_C) ||                           \
    (TEMPERATURE_HOT_WARNING_THRESH_C + 1 >= TEMPERATURE_SHUTDOWN_THRESH_C)
#error "Invalid leaky-bucket parameters or virtual temperature"
#endif

#if (LEAKY_BUCKET_LEAK_MW < 60000UL) || (LEAKY_BUCKET_LEAK_MW >= 80000UL) ||                            \
    (LEAKY_BUCKET_COOLING_TIME_MS < 10000UL) || (LEAKY_BUCKET_COOLING_TIME_MS > 1000000UL)
#error "Invalid leaky-bucket drain or cooling time"
#endif

/* The regular build owns PA13 through the TIM16/TIM17 IR_OUT PWM path. The
 * fallback build overrides this to zero and retains only direct GPIO modes. */
#ifndef FAN_PWM_ENABLED
#define FAN_PWM_ENABLED 1
#endif

#define FAN_ADAPTIVE_ON_TEMPERATURE_C   40
#define FAN_COOL_ON_TEMPERATURE_C       50
#define FAN_QUIET_ON_TEMPERATURE_C      70
#define FAN_TEMPERATURE_HYSTERESIS_C    2
#define FAN_MINIMUM_PWM_PERCENT         25
#define FAN_RAMP_PERCENT_PER_SECOND     25
#define FAN_STARTUP_BOOST_TIME_MS       500
#define FAN_ADAPTIVE_UPDATE_INTERVAL_MS 1000
#define FAN_MINIMUM_ON_TIME_MS          (10 * 1000)
#define FAN_MINIMUM_OFF_TIME_MS         (5 * 1000)

/* Leave PA13 under SWD control and defer firmware fan commands during this
 * boot window. Set to zero through a build flag when immediate fan takeover
 * is preferred over a guaranteed debugger-connection interval. */
#ifndef FAN_STARTUP_OFF_TIME_MS
#define FAN_STARTUP_OFF_TIME_MS (5 * 1000)
#endif

#if (FAN_PWM_ENABLED != 0) && (FAN_PWM_ENABLED != 1)
#error "FAN_PWM_ENABLED must be 0 or 1"
#endif

#if (FAN_ADAPTIVE_ON_TEMPERATURE_C < FAN_TEMPERATURE_HYSTERESIS_C) ||                                                  \
    (FAN_COOL_ON_TEMPERATURE_C < FAN_TEMPERATURE_HYSTERESIS_C) ||                                                      \
    (FAN_QUIET_ON_TEMPERATURE_C < FAN_TEMPERATURE_HYSTERESIS_C) || (FAN_MINIMUM_PWM_PERCENT == 0) ||                   \
    (FAN_MINIMUM_PWM_PERCENT > 100) || (FAN_RAMP_PERCENT_PER_SECOND == 0) || (FAN_RAMP_PERCENT_PER_SECOND > 100) ||    \
    (FAN_STARTUP_BOOST_TIME_MS == 0) || (FAN_ADAPTIVE_UPDATE_INTERVAL_MS == 0) || (FAN_MINIMUM_ON_TIME_MS == 0) ||     \
    (FAN_MINIMUM_OFF_TIME_MS == 0)
#error "Invalid fan thresholds, duty limits, or timing"
#endif

/* Set to 0 if production units intentionally omit both external NTC sensors. */
#ifndef NTC_FAULT_WARNING_ENABLED
#define NTC_FAULT_WARNING_ENABLED 1
#endif

#if (NTC_FAULT_WARNING_ENABLED != 0) && (NTC_FAULT_WARNING_ENABLED != 1)
#error "NTC_FAULT_WARNING_ENABLED must be 0 or 1"
#endif

#if (TEMPERATURE_HYSTERYSIS_C > TEMPERATURE_HOT_WARNING_THRESH_C) ||                                                   \
    (TEMPERATURE_HOT_WARNING_THRESH_C >= TEMPERATURE_SHUTDOWN_THRESH_C) || (TEMPERATURE_SHUTDOWN_TIME_MS == 0)
#error "Invalid thermal thresholds, hysteresis, or shutdown timing"
#endif

#define DC_UNDERVOLTAGE_FAULT_MV 14000

#if (DC_UNDERVOLTAGE_FAULT_MV == 0) || (DC_UNDERVOLTAGE_FAULT_MV > 65535)
#error "DC_UNDERVOLTAGE_FAULT_MV must fit in millivolts"
#endif

#ifndef PWRMGT_POWER_LOSS_SAMPLE_INTERVAL_MS
#define PWRMGT_POWER_LOSS_SAMPLE_INTERVAL_MS 20
#endif

/* Power-loss protection intentionally compares raw 10-bit DC-input ADC
 * samples. With the fixed 22K/2K2 divider and 3.3 V ADC reference, one count
 * represents about 35.5 mV at DC-IN. These defaults approximate the former
 * 1000 mV fast, 300 mV sustained, and 75 mV segment thresholds. */
#ifndef PWRMGT_POWER_LOSS_FAST_DROP_ADC_COUNTS
#define PWRMGT_POWER_LOSS_FAST_DROP_ADC_COUNTS 28
#endif

#ifndef PWRMGT_POWER_LOSS_SUSTAINED_INTERVAL_COUNT
#define PWRMGT_POWER_LOSS_SUSTAINED_INTERVAL_COUNT 3
#endif

#ifndef PWRMGT_POWER_LOSS_SUSTAINED_DROP_ADC_COUNTS
#define PWRMGT_POWER_LOSS_SUSTAINED_DROP_ADC_COUNTS 8
#endif

#ifndef PWRMGT_POWER_LOSS_MIN_SEGMENT_DROP_ADC_COUNTS
#define PWRMGT_POWER_LOSS_MIN_SEGMENT_DROP_ADC_COUNTS 2
#endif

#if (PWRMGT_POWER_LOSS_SAMPLE_INTERVAL_MS == 0) || (PWRMGT_POWER_LOSS_SAMPLE_INTERVAL_MS > 1000)
#error "PWRMGT_POWER_LOSS_SAMPLE_INTERVAL_MS must be between 1 and 1000 milliseconds"
#endif

#if (PWRMGT_POWER_LOSS_FAST_DROP_ADC_COUNTS == 0) || (PWRMGT_POWER_LOSS_FAST_DROP_ADC_COUNTS > 1023) ||                \
    (PWRMGT_POWER_LOSS_SUSTAINED_DROP_ADC_COUNTS == 0) || (PWRMGT_POWER_LOSS_SUSTAINED_DROP_ADC_COUNTS > 1023) ||      \
    (PWRMGT_POWER_LOSS_MIN_SEGMENT_DROP_ADC_COUNTS == 0) || (PWRMGT_POWER_LOSS_MIN_SEGMENT_DROP_ADC_COUNTS > 1023)
#error "Power-loss voltage drops must fit in nonzero 10-bit ADC counts"
#endif

#if (PWRMGT_POWER_LOSS_SUSTAINED_INTERVAL_COUNT < 2) || (PWRMGT_POWER_LOSS_SUSTAINED_INTERVAL_COUNT > 10)
#error "PWRMGT_POWER_LOSS_SUSTAINED_INTERVAL_COUNT must be between 2 and 10"
#endif

/* Buck overvoltage protection compares the unfiltered 10-bit ADC sample.
 * With the fixed 22K/2K2 divider and 3.3 V ADC reference */
#ifndef PWRMGT_BUCK_VOLTAGE_SPIKE_MV
#define PWRMGT_BUCK_VOLTAGE_SPIKE_MV 25000UL
#endif

#ifndef PWRMGT_BUCK_VOLTAGE_SPIKE_ADC_COUNTS
#define PWRMGT_BUCK_VOLTAGE_SPIKE_ADC_COUNTS ADC_VOLTAGE_TO_COUNTS(PWRMGT_BUCK_VOLTAGE_SPIKE_MV)
#endif

#if (PWRMGT_BUCK_VOLTAGE_SPIKE_MV == 0) || (PWRMGT_BUCK_VOLTAGE_SPIKE_ADC_COUNTS > ADC_FULL_SCALE)
#error "Buck voltage-spike threshold must be nonzero and fit in the ADC input range"
#endif

#define DC_HIGH_POWER_MINIMUM_MV    19000
#define DC_HIGH_POWER_HYSTERESIS_MV 1000

#if (DC_HIGH_POWER_MINIMUM_MV <= 0) || (DC_HIGH_POWER_MINIMUM_MV > 65535) || (DC_HIGH_POWER_HYSTERESIS_MV < 0) ||      \
    ((DC_HIGH_POWER_MINIMUM_MV + DC_HIGH_POWER_HYSTERESIS_MV) > 65535)
#error "Invalid high-power DC threshold or hysteresis"
#endif

#ifndef PWRLVL_CURRENT_LIMIT_ENABLED
#define PWRLVL_CURRENT_LIMIT_ENABLED 1
#endif

#if PWRLVL_CURRENT_LIMIT_ENABLED
#define PWRLVL_CURRENT_LIMIT_MA 5200
#endif

#define PWRLVL_SHORT_CIRCUIT_CURRENT_MA 5800
#define PWRLVL_SHORT_CIRCUIT_TIME_MS    5000

#if (PWRLVL_SHORT_CIRCUIT_CURRENT_MA == 0) || (PWRLVL_SHORT_CIRCUIT_CURRENT_MA > 65535)
#error "PWRLVL_SHORT_CIRCUIT_CURRENT_MA must fit in milliamps"
#endif

#if PWRLVL_SHORT_CIRCUIT_TIME_MS == 0
#error "PWRLVL_SHORT_CIRCUIT_TIME_MS must be nonzero"
#endif

// -----------------------------------------------------------------------------
// Battery Configuration
// -----------------------------------------------------------------------------

#define BATTERY_MINIMUM_CELL_CNT_LIPO 4
#define BATTERY_MAXIMUM_CELL_CNT_LIPO 8

#define BATTERY_MINIMUM_CELL_CNT_LIHV 4
#define BATTERY_MAXIMUM_CELL_CNT_LIHV 8

#define BATTERY_MINIMUM_CELL_CNT_LIFE 6
#define BATTERY_MAXIMUM_CELL_CNT_LIFE 9

#if (BATTERY_MINIMUM_CELL_CNT_LIPO == 0) || (BATTERY_MINIMUM_CELL_CNT_LIPO > BATTERY_MAXIMUM_CELL_CNT_LIPO) ||         \
    (BATTERY_MINIMUM_CELL_CNT_LIHV == 0) || (BATTERY_MINIMUM_CELL_CNT_LIHV > BATTERY_MAXIMUM_CELL_CNT_LIHV) ||         \
    (BATTERY_MINIMUM_CELL_CNT_LIFE == 0) || (BATTERY_MINIMUM_CELL_CNT_LIFE > BATTERY_MAXIMUM_CELL_CNT_LIFE)
#error "Invalid battery chemistry cell-count limits"
#endif

#if (BATTERY_MAXIMUM_CELL_CNT_LIPO > 255) || (BATTERY_MAXIMUM_CELL_CNT_LIHV > 255) ||                                  \
    (BATTERY_MAXIMUM_CELL_CNT_LIFE > 255)
#error "Battery cell-count limits must fit in uint8_t"
#endif

#define BATTERY_OVERRIDE_MINIMUM_MV 14000

#if (BATTERY_OVERRIDE_MINIMUM_MV == 0) || (BATTERY_OVERRIDE_MINIMUM_MV > 65535)
#error "BATTERY_OVERRIDE_MINIMUM_MV must fit in millivolts"
#endif

// -----------------------------------------------------------------------------
// Display
// -----------------------------------------------------------------------------

#define OLED_DIM_CONTRAST 32

/* Horizontal burn-in shifts for the two fixed-width OLED fonts. */
#define OLED_MAX_PIXEL_SHIFT_X_SMALLFONT 7
#define OLED_MAX_PIXEL_SHIFT_X_BIGFONT   3
#define OLED_MAX_PIXEL_SHIFT_Y           3

/* Portrait power graph: 28 text pixels plus a 100-pixel, 0-100 W plot. */
/* The 16-entry ring retains each x ms interval peak, including the current interval. */
/* Rendering shows live power in the center pair and mirrors the 15 completed peaks outward. */
#define PWRMGT_GRAPH_TEXT_HEIGHT_PX     28
#define PWRMGT_GRAPH_UPDATE_INTERVAL_MS 250
#define PWRMGT_GRAPH_MAX_POWER_MW       100000

#if PWRMGT_GRAPH_TEXT_HEIGHT_PX >= 128
#error "PWRMGT_GRAPH_TEXT_HEIGHT_PX must leave room for the graph"
#endif

#if PWRMGT_GRAPH_UPDATE_INTERVAL_MS == 0
#error "PWRMGT_GRAPH_UPDATE_INTERVAL_MS must be nonzero"
#endif

#if PWRMGT_GRAPH_MAX_POWER_MW == 0
#error "PWRMGT_GRAPH_MAX_POWER_MW must be nonzero"
#endif

// -----------------------------------------------------------------------------
// Boot Power Qualification
// -----------------------------------------------------------------------------

#define BOOT_POWER_WAIT_MS    300
#define BOOT_POWER_STABLE_MS  100
#define BOOT_POWER_TIMEOUT_MS 2000

#if (BOOT_POWER_WAIT_MS == 0) || (BOOT_POWER_STABLE_MS == 0) || (BOOT_POWER_TIMEOUT_MS == 0)
#error "Boot power timing values must be nonzero"
#endif

#if (BOOT_POWER_WAIT_MS >= BOOT_POWER_TIMEOUT_MS) || (BOOT_POWER_STABLE_MS >= BOOT_POWER_TIMEOUT_MS)
#error "Boot power wait and stability times must be shorter than its timeout"
#endif
