frank26080115/Hot-Wand/firmware/src/splash.c

#include "splash.h"

const uint8_t splash_flame1[SPLASH_BITMAP_BYTES] = {
    0x00, 0x80, 0x00, 0x00, 0x00, 0x80, 0x00, 0x00, 0x00, 0x00, 0x00, 0x00, 0x00, 0x00, 0x00, 0x00, 0x00, 0x80, 0x00,
    0x00, 0x00, 0x00, 0x00, 0x00, 0x00, 0x00, 0x00, 0x00, 0x00, 0x80, 0x01, 0x00, 0x00, 0x00, 0x00, 0x00, 0x00, 0x40,
    0x00, 0x00, 0x00, 0xc0, 0x00, 0x00, 0x00, 0x40, 0x00, 0x00, 0x00, 0x40, 0x00, 0x00, 0x00, 0xc0, 0x40, 0x00, 0x00,
    0x60, 0xc0, 0x00, 0x00, 0xc0, 0x00, 0x00, 0x00, 0xe2, 0x00, 0x00, 0x00, 0xc0, 0x01, 0x00, 0x00, 0xe0, 0x40, 0x00,
    0x00, 0xc0, 0x03, 0x00, 0x00, 0xc0, 0x01, 0x00, 0x00, 0xc0, 0x03, 0x00, 0x00, 0x84, 0x4f, 0x00, 0x00, 0x88, 0x07,
    0x00, 0x00, 0x00, 0x4f, 0x00, 0x00, 0x08, 0x4f, 0x00, 0x00, 0x00, 0x5e, 0x00, 0x00, 0x10, 0x5e, 0x00, 0x00, 0x00,
    0x5c, 0x00, 0x20, 0x00, 0x3e, 0x00, 0x10, 0x20, 0x7c, 0x00, 0x00, 0x20, 0x7e, 0x00, 0x00, 0x00, 0x3e, 0x00, 0x00,
    0x20, 0x77, 0x02, 0x00, 0x40, 0x3e, 0x00, 0x00, 0x20, 0x1f, 0x00, 0x20, 0x84, 0x1f, 0x02, 0x00, 0x44, 0x1f, 0x00,
    0x20, 0xc8, 0x17, 0x00, 0x40, 0xc4, 0x05, 0x20, 0x00, 0xe4, 0x07, 0x20, 0x00, 0xe2, 0x86, 0x01, 0x20, 0xf2, 0x81,
    0x00, 0x00, 0xfa, 0x02, 0x00, 0x00, 0x73, 0x43, 0x10, 0x00, 0xf7, 0x01, 0x10, 0x00, 0x7f, 0x03, 0x00, 0x00, 0xf7,
    0x2a, 0x08, 0x00, 0xdf, 0x07, 0x08, 0x00, 0xdf, 0x26, 0x08, 0x00, 0x7f, 0x25, 0x08, 0x00, 0xfe, 0x2e, 0x04, 0x00,
    0xfe, 0x4e, 0x00, 0x00, 0xee, 0x6d, 0x00, 0x00, 0xec, 0x4d, 0x00, 0x10, 0xec, 0xdb, 0x00, 0x30, 0xc8, 0x5f, 0x00,
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
    0x9b, 0x01, 0x40, 0xec, 0x37, 0x06, 0x10, 0xf2, 0x6d, 0x08, 0x00, 0x89, 0x95, 0x00, 0x00, 0x28, 0x84, 0x00,
};

const uint8_t* const splash_screens[SPLASH_SCREEN_COUNT] = {
    splash_flame1,
    splash_flame2,
    splash_pcb1,
    splash_pcb2,
    splash_spark1,
};
