frank26080115/Hot-Wand/firmware-lite/inc/hotwandlite.h

#pragma once

#include <stdint.h>
#include <stdbool.h>

// Umbrella include for the complete Hot Wand Lite firmware interface.

#include "pins.h"

#include "blink.h"
#include "power.h"
#include "rfgen.h"
#include "watchdog.h"
