frank26080115/Hot-Wand/firmware/src/splash_fiducial.c

#include "splash.h"

/* Generated from art/raw/fiducial.png by art/png2bin/png2bin.exe.
 * The converter output begins with width and height; this array omits those two bytes.
 * XBM stores each row leftmost pixel in the least-significant bit.
 */
#if defined(HOT_WAND_VISION_TEST) && HOT_WAND_VISION_TEST
const uint8_t splash_fiducial[SPLASH_BITMAP_BYTES] = {
    0x0f, 0x0f, 0xf0, 0xf0, 0x0f, 0x0f, 0xf0, 0xf0, 0x0f, 0x0f, 0xf0, 0xf0, 0x0f, 0x0f, 0xf0, 0xf0,
    0xf0, 0x00, 0x00, 0x0f, 0xf0, 0x00, 0x00, 0x0f, 0xf0, 0x00, 0x00, 0x0f, 0xf0, 0x00, 0x00, 0x0f,
    0x0f, 0x00, 0x00, 0xf0, 0x0f, 0x00, 0x00, 0xf0, 0x0f, 0x00, 0x00, 0xf0, 0x0f, 0x00, 0x00, 0xf0,
    0x00, 0x00, 0x00, 0x00, 0x00, 0x00, 0x00, 0x00, 0x00, 0x00, 0x00, 0x00, 0x00, 0x00, 0x00, 0x00,
    0x00, 0x00, 0x00, 0x00, 0x00, 0x00, 0x00, 0x00, 0x00, 0x00, 0x00, 0x00, 0x00, 0x00, 0x00, 0x00,
    0x00, 0x00, 0x00, 0x00, 0x00, 0x00, 0x00, 0x00, 0x00, 0x00, 0x00, 0x00, 0x00, 0x00, 0x00, 0x00,
    0x00, 0x00, 0x00, 0x00, 0x00, 0x00, 0x00, 0x00, 0x00, 0x00, 0x00, 0x00, 0x00, 0x00, 0x00, 0x00,
    0x00, 0x00, 0x00, 0x00, 0x00, 0x00, 0x00, 0x00, 0x00, 0x00, 0x00, 0x00, 0x00, 0x00, 0x00, 0x00,
    0x00, 0x00, 0x00, 0x00, 0x00, 0x00, 0x00, 0x00, 0x00, 0x00, 0x00, 0x00, 0x00, 0x00, 0x00, 0x00,
    0x00, 0x00, 0x00, 0x00, 0x00, 0x00, 0x00, 0x00, 0x00, 0x00, 0x00, 0x00, 0x00, 0x00, 0x00, 0x00,
    0x00, 0x00, 0x00, 0x00, 0x00, 0x00, 0x00, 0x00, 0x00, 0x00, 0x00, 0x00, 0x00, 0x00, 0x00, 0x00,
    0x00, 0x00, 0x00, 0x00, 0x00, 0x00, 0x00, 0x00, 0x00, 0x00, 0x00, 0x00, 0x00, 0xa0, 0x0a, 0x00,
    0x00, 0xa0, 0x0a, 0x00, 0x00, 0xa0, 0x0a, 0x00, 0x00, 0xa0, 0x0a, 0x00, 0x00, 0xa0, 0x0a, 0x00,
    0x00, 0xa0, 0x0a, 0x00, 0x00, 0xa0, 0x0a, 0x00, 0x00, 0xa0, 0x0a, 0x00, 0x00, 0xa0, 0x0a, 0x00,
    0x00, 0xa0, 0x0a, 0x00, 0x00, 0xa0, 0x0a, 0x00, 0x00, 0xa0, 0x0a, 0x00, 0x00, 0xa0, 0x0a, 0x00,
    0xff, 0xff, 0xff, 0xff, 0x00, 0xa0, 0x0a, 0x00, 0xff, 0xff, 0xff, 0xff, 0x00, 0xa0, 0x0a, 0x00,
    0xff, 0xff, 0xff, 0xff, 0x00, 0xa0, 0x0a, 0x00, 0xff, 0xff, 0xff, 0xff, 0x00, 0xa0, 0x0a, 0x00,
    0x00, 0xa0, 0x0a, 0x00, 0x00, 0xa0, 0x0a, 0x00, 0x00, 0xa0, 0x0a, 0x00, 0x00, 0xa0, 0x0a, 0x00,
    0x00, 0xa0, 0x0a, 0x00, 0x00, 0xa0, 0x0a, 0x00, 0x00, 0xa0, 0x0a, 0x00, 0x00, 0xa0, 0x0a, 0x00,
    0x00, 0xa0, 0x0a, 0x00, 0x00, 0xa0, 0x0a, 0x00, 0x00, 0xa0, 0x0a, 0x00, 0x00, 0x00, 0x00, 0x00,
    0x00, 0x00, 0x00, 0x00, 0x00, 0x00, 0x00, 0x00, 0x00, 0x00, 0x00, 0x00, 0x00, 0x00, 0x00, 0x00,
    0x00, 0x00, 0x00, 0x00, 0x00, 0x00, 0x00, 0x00, 0x00, 0x00, 0x00, 0x00, 0x00, 0x00, 0x00, 0x00,
    0x00, 0x00, 0x00, 0x00, 0x00, 0x00, 0x00, 0x00, 0x00, 0x00, 0x00, 0x00, 0x00, 0x00, 0x00, 0x00,
    0x00, 0x00, 0x00, 0x00, 0x00, 0x00, 0x00, 0x00, 0x00, 0x00, 0x00, 0x00, 0x00, 0x00, 0x00, 0x00,
    0x00, 0x00, 0x00, 0x00, 0x00, 0x00, 0x00, 0x00, 0x00, 0x00, 0x00, 0x00, 0x00, 0x00, 0x00, 0x00,
    0x00, 0x00, 0x00, 0x00, 0x00, 0x00, 0x00, 0x00, 0x00, 0x00, 0x00, 0x00, 0x00, 0x00, 0x00, 0x00,
    0x00, 0x00, 0x00, 0x00, 0x00, 0x00, 0x00, 0x00, 0x00, 0x00, 0x00, 0x00, 0x00, 0x00, 0x00, 0x00,
    0x00, 0x00, 0x00, 0x00, 0x00, 0x00, 0x00, 0x00, 0x00, 0x00, 0x00, 0x00, 0x00, 0x00, 0x00, 0x00,
    0x00, 0x00, 0x00, 0x00, 0x00, 0x00, 0x00, 0x00, 0x00, 0x00, 0x00, 0x00, 0x00, 0x00, 0x00, 0x00,
    0x0f, 0x00, 0x00, 0xf0, 0x0f, 0x00, 0x00, 0xf0, 0x0f, 0x00, 0x00, 0xf0, 0x0f, 0x00, 0x00, 0xf0,
    0xf0, 0x00, 0x00, 0x0f, 0xf0, 0x00, 0x00, 0x0f, 0xf0, 0x00, 0x00, 0x0f, 0xf0, 0x00, 0x00, 0x0f,
    0x0f, 0x0f, 0xf0, 0xf0, 0x0f, 0x0f, 0xf0, 0xf0, 0x0f, 0x0f, 0xf0, 0xf0, 0x0f, 0x0f, 0xf0, 0xf0,
};
#endif
