frank26080115/Hot-Wand/firmware/inc/oled.h

#pragma once

#include "hotwand.h"
#include "stm32f0xx_hal.h"
#include "u8g2.h"

#include <stdbool.h>
#include <stdint.h>

#define OLED_I2C_ADDRESS_7BIT      0x3C
#define OLED_I2C_ADDRESS_U8G2      ((uint8_t)(OLED_I2C_ADDRESS_7BIT << 1))
#define OLED_I2C_TRANSFER_CAPACITY 32

typedef enum
{
    OLED_ERROR_NONE = 0,
    OLED_ERROR_TRANSFER_STATE,
    OLED_ERROR_TRANSFER_CAPACITY,
    OLED_ERROR_I2C_NACK,
    OLED_ERROR_I2C_BUS,
    OLED_ERROR_I2C_ARBITRATION,
    OLED_ERROR_I2C_OVERRUN,
    OLED_ERROR_I2C_UNEXPECTED_STOP,
    OLED_ERROR_I2C_TX_TIMEOUT,
    OLED_ERROR_I2C_STOP_TIMEOUT
} OLED_Error;

typedef struct
{
    u8g2_t             graphics;
    I2C_HandleTypeDef* i2c;
    uint32_t           last_i2c_status;
    OLED_Error         error;
    uint8_t            transfer_buffer[OLED_I2C_TRANSFER_CAPACITY];
    uint8_t            transfer_length;
    uint8_t            transfer_active;
    uint8_t            transport_ok;
    uint8_t            initialized;
    uint8_t            dimmed;
} OLED_Handle;

extern I2C_HandleTypeDef i2c1;
extern OLED_Handle       oled;

void    I2C1_Init(void);
void    HAL_I2C_MspInit(I2C_HandleTypeDef* handle);
bool    OLED_Init(OLED_Handle* oled, I2C_HandleTypeDef* i2c);
void    OLED_ConfigureGraphics(OLED_Handle* oled);
u8g2_t* OLED_GetGraphics(OLED_Handle* oled);
bool    OLED_SendBuffer(OLED_Handle* oled);
bool    OLED_SetDimMode(OLED_Handle* oled, bool dimmed);
void    show_splash(void);
#if defined(HOT_WAND_VISION_TEST) && HOT_WAND_VISION_TEST
#define OLED_VISION_FRAMEBUFFER_BYTES 512
/* Even generation means the mirror contains one completed OLED send. */
extern volatile uint32_t vision_test_oled_sent_generation;
extern volatile uint8_t  vision_test_oled_sent_framebuffer[OLED_VISION_FRAMEBUFFER_BYTES];
void    OLED_ShowFiducial(void);
#endif
