frank26080115/Hot-Wand/firmware/inc/fan.h

#pragma once

#include "hotwand.h"

#ifdef __cplusplus
extern "C"
{
#endif

/* Returns a mode supported by the selected build. Unsupported fallback-build
 * modes become the automatic cool profile. */
uint8_t fan_normalize_mode(uint8_t mode);
/* Initializes the saved FAN_MODE_* and the selected PA13 signal topology. */
void fan_init(uint8_t mode, bool signal_inverted);
/* Performs the optional delayed, one-shot external NTC health warning. */
void ntc_task(void);
void fan_task(void);
void fan_on_wake(void);
/* Stops the fan and prevents fan_task() from restarting it. */
void fan_stop(void);
/* Re-enables fan_task() after a recoverable stop, preserving the configured mode. */
void fan_resume(void);

#ifdef __cplusplus
}
#endif
