frank26080115/Hot-Wand/firmware/inc/defs.h

#pragma once

/*
use this file to define unchanging constants
*/
enum
{
    U8G2_DRAW_CLEAR          = 0,
    U8G2_DRAW_SET            = 1,
    U8G2_DRAW_XOR            = 2,
    OLED_FIRST_TEXT_BASELINE = 9,
    OLED_TEXT_LINE_HEIGHT    = 10,
};
